Liiiin-hku/smart-scallion-harvester-planter/cad/大葱收种一体机/车架.step

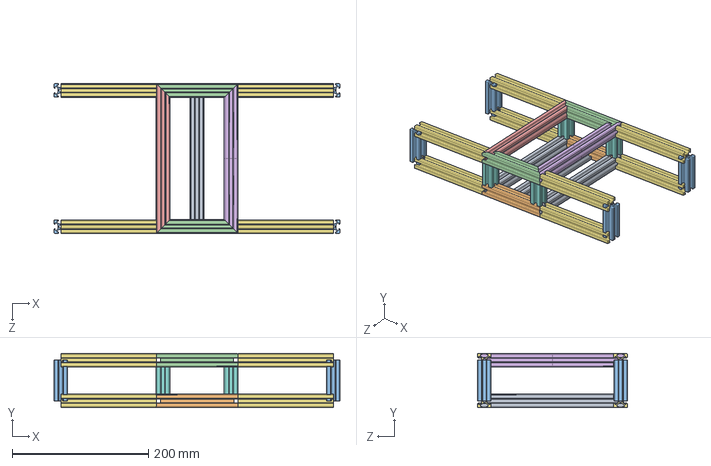
[picture p16: CAD file, 2026-09-12]
cad/大葱收种一体机/车架.step
420.0 x 80.0 x 220.3 mm
