Liiiin-hku/smart-scallion-harvester-planter/cad/大葱收种一体机/不锈钢迷你型CTMA系列气缸[CTMA-16x25-S-CA-SDB]/不锈钢迷你型CTMA系列气缸[CTMA-16x25-S-CA-SDB]_SDB.SLDPRT

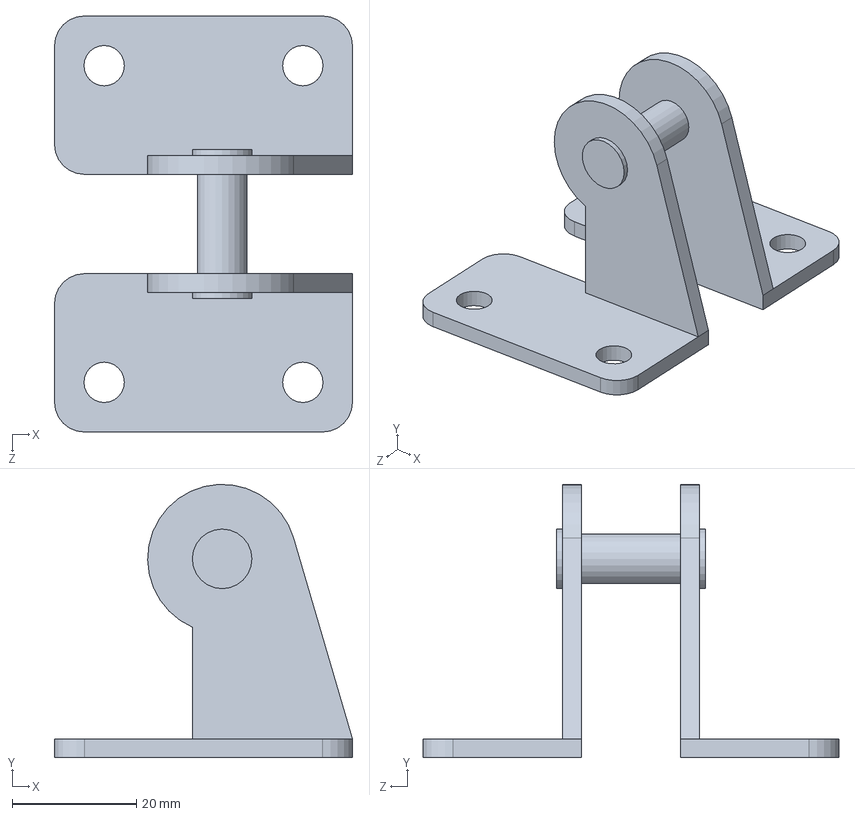
[picture p17: CAD file, 2026-09-12]
cad/大葱收种一体机/不锈钢迷你型CTMA系列气缸[CTMA-16x25-S-CA-SDB]/不锈钢迷你型CTMA系列气缸[CTMA-16x25-S-CA-SDB]_SDB.SLDPRT
48.0 x 44.0 x 67.0 mm
