Liiiin-hku/smart-scallion-harvester-planter/cad/大葱收种一体机/标件/GB╱T 70.2-2015[内六角平圆头螺钉M4×30].step

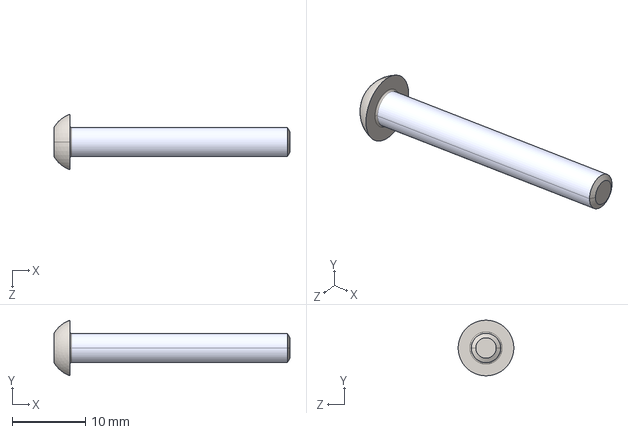
[picture p18: CAD file, 2026-09-12]
cad/大葱收种一体机/标件/GB╱T 70.2-2015[内六角平圆头螺钉M4×30].step
32.2 x 7.60 x 7.60 mm
