Liiiin-hku/smart-scallion-harvester-planter/cad/大葱收种一体机/轮子/21. TYRE.SLDPRT

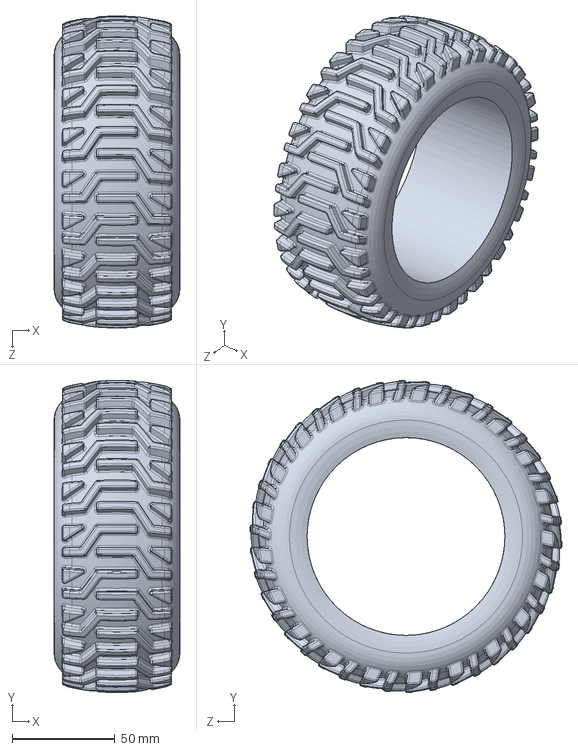
[picture p19: CAD file, 2026-09-12]
cad/大葱收种一体机/轮子/21. TYRE.SLDPRT
61.1 x 151.6 x 151.5 mm
