Liiiin-hku/smart-scallion-harvester-planter/cad/大葱收种一体机/16缸体.step

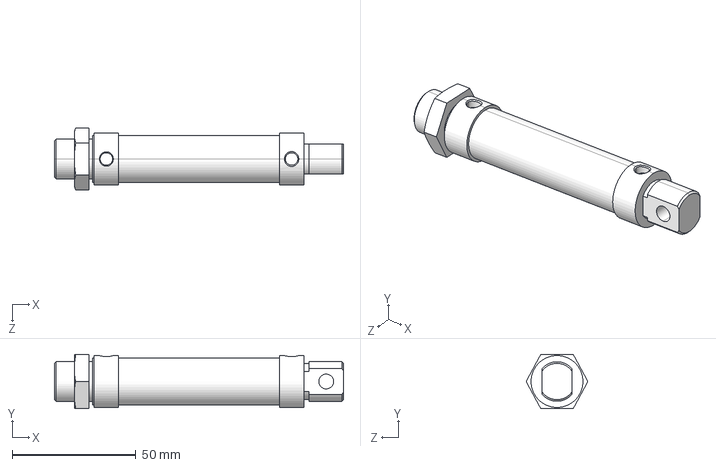
[picture p20: CAD file, 2026-09-12]
cad/大葱收种一体机/16缸体.step
117.0 x 22.0 x 25.0 mm
