Liiiin-hku/smart-scallion-harvester-planter/cad/大葱收种一体机/不锈钢迷你型CTMA系列气缸[CTMA-16x25-S-CA-SDB]/后LB.SLDPRT

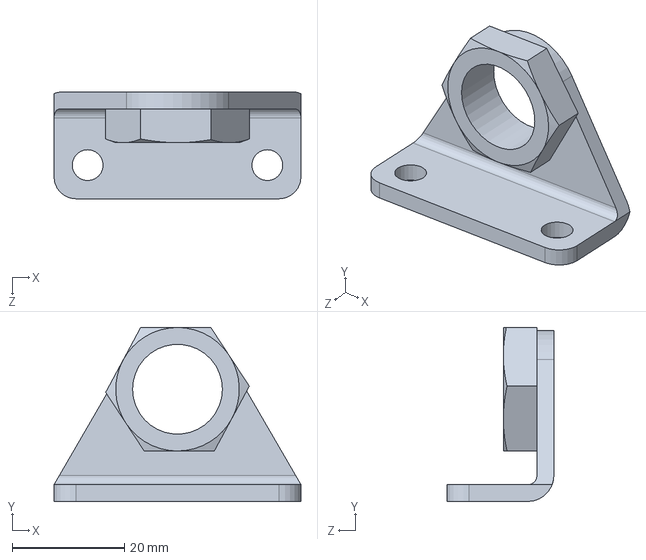
[picture p21: CAD file, 2026-09-12]
cad/大葱收种一体机/不锈钢迷你型CTMA系列气缸[CTMA-16x25-S-CA-SDB]/后LB.SLDPRT
44.0 x 31.0 x 19.0 mm
