Liiiin-hku/smart-scallion-harvester-planter/cad/大葱收种一体机/轮子/19.AXLE.SLDPRT

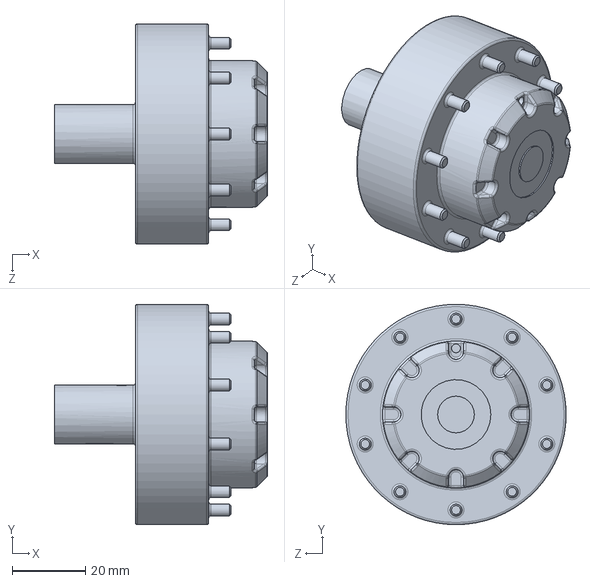
[picture p22: CAD file, 2026-09-12]
cad/大葱收种一体机/轮子/19.AXLE.SLDPRT
58.0 x 60.0 x 60.0 mm
