Liiiin-hku/smart-scallion-harvester-planter/cad/大葱收种一体机/不锈钢迷你型CTMA系列气缸[CTMA-16x25-S-CA-SDB]/活塞杆.SLDPRT

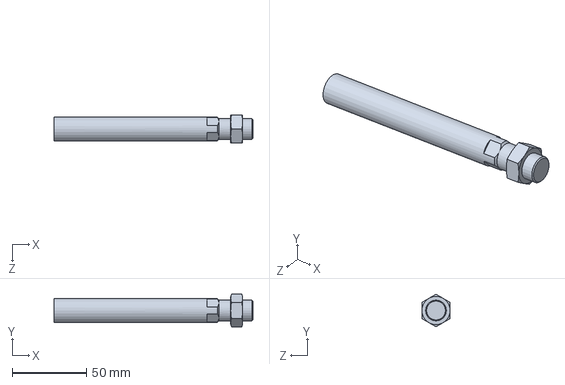
[picture p23: CAD file, 2026-09-12]
cad/大葱收种一体机/不锈钢迷你型CTMA系列气缸[CTMA-16x25-S-CA-SDB]/活塞杆.SLDPRT
134.0 x 21.9 x 19.0 mm
