Liiiin-hku/smart-scallion-harvester-planter/cad/大葱收种一体机/播苗盘.step

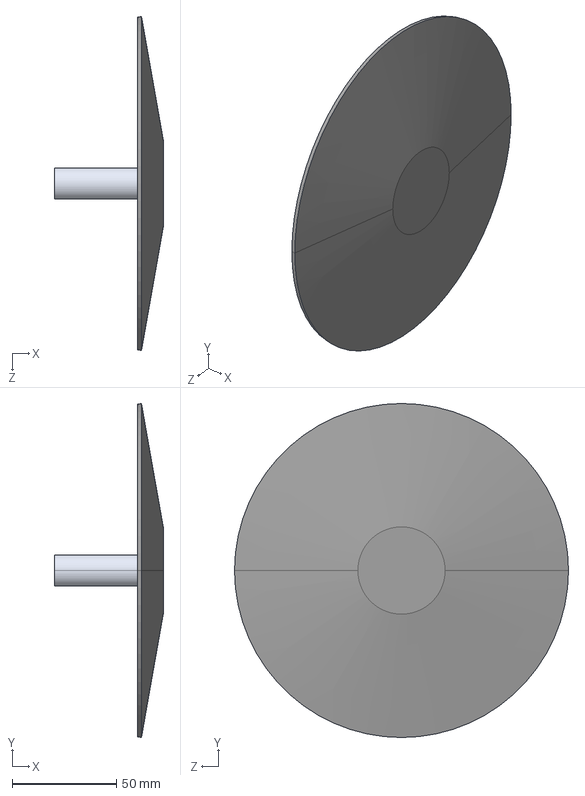
[picture p24: CAD file, 2026-09-12]
cad/大葱收种一体机/播苗盘.step
52.0 x 160.0 x 160.0 mm
