Liiiin-hku/smart-scallion-harvester-planter/cad/大葱收种一体机/标件/GB╱T 276-2013[一面带密封圈（非接触式）的深沟球轴承[60000-RZ]619／6-RZ].step

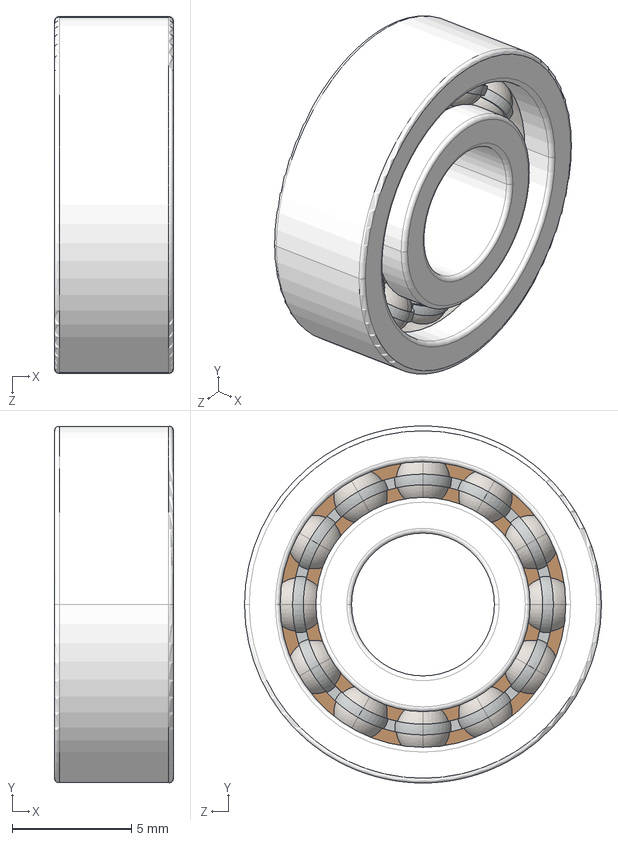
[picture p25: CAD file, 2026-09-12]
cad/大葱收种一体机/标件/GB╱T 276-2013[一面带密封圈（非接触式）的深沟球轴承[60000-RZ]619／6-RZ].step
5.00 x 15.0 x 15.0 mm
