Liiiin-hku/smart-scallion-harvester-planter/cad/大葱收种一体机/轮子/20.RIM.SLDPRT

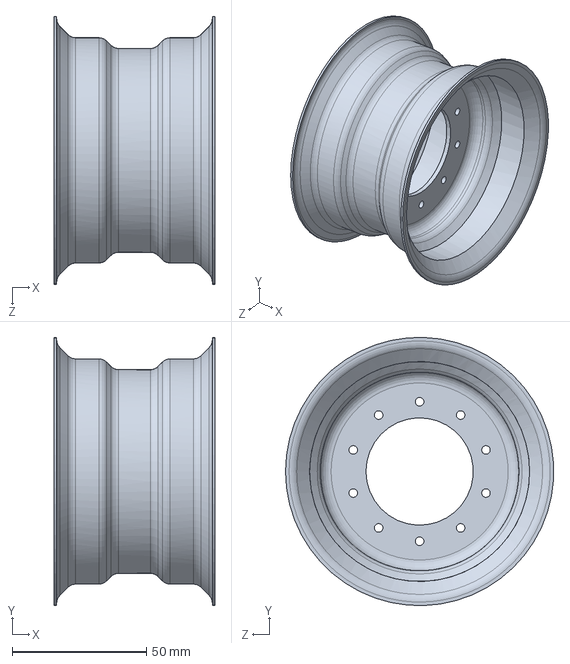
[picture p26: CAD file, 2026-09-12]
cad/大葱收种一体机/轮子/20.RIM.SLDPRT
60.0 x 100.0 x 99.9 mm
