Liiiin-hku/smart-scallion-harvester-planter/cad/大葱收种一体机/1X10X30.step

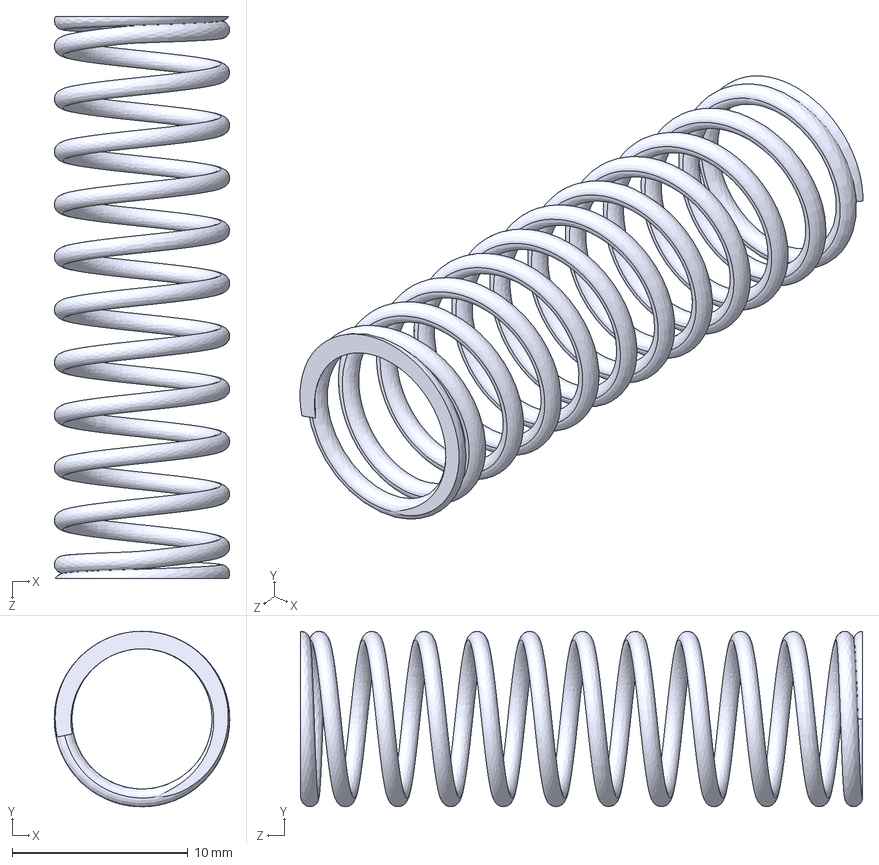
[picture p27: CAD file, 2026-09-12]
cad/大葱收种一体机/1X10X30.step
10.00 x 10.00 x 32.0 mm
