Liiiin-hku/smart-scallion-harvester-planter/cad/大葱收种一体机/不锈钢迷你型CTMA系列气缸[CTMA-16x25-S-CA-SDB]/不锈钢迷你型CTMA系列气缸[CTMA-16x25-S-CA-SDB]_16缸体.SLDPRT

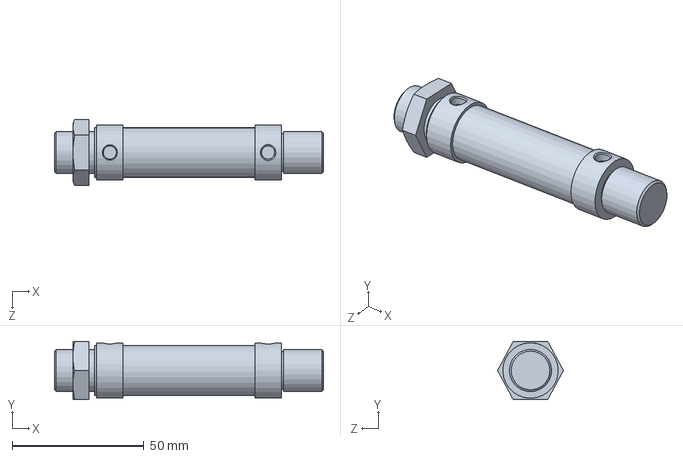
[picture p28: CAD file, 2026-09-12]
cad/大葱收种一体机/不锈钢迷你型CTMA系列气缸[CTMA-16x25-S-CA-SDB]/不锈钢迷你型CTMA系列气缸[CTMA-16x25-S-CA-SDB]_16缸体.SLDPRT
102.0 x 22.0 x 25.0 mm
