Liiiin-hku/smart-scallion-harvester-planter/cad/大葱收种一体机/盘.step

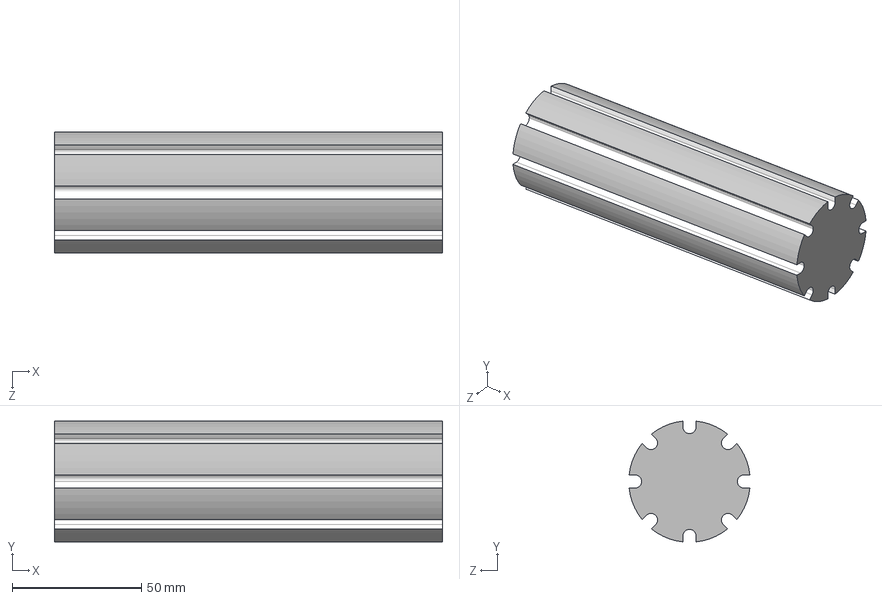
[picture p29: CAD file, 2026-09-12]
cad/大葱收种一体机/盘.step
150.0 x 46.7 x 46.7 mm
