Liiiin-hku/smart-scallion-harvester-planter/cad/大葱收种一体机/不锈钢迷你型CTMA系列气缸[CTMA-16x25-S-CA-SDB]/不锈钢迷你型CTMA系列气缸[CTMA-16x25-S-CA-SDB]_16活塞杆.SLDPRT

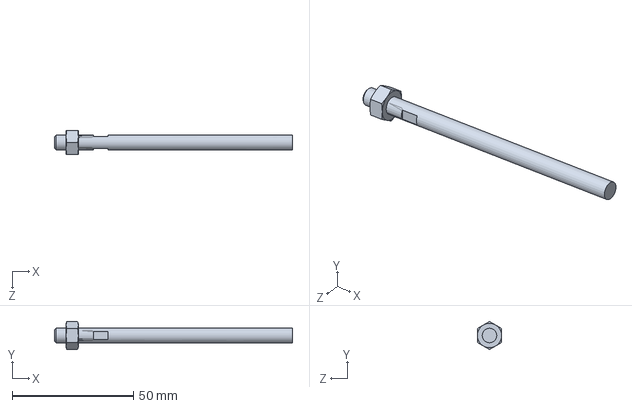
[picture p30: CAD file, 2026-09-12]
cad/大葱收种一体机/不锈钢迷你型CTMA系列气缸[CTMA-16x25-S-CA-SDB]/不锈钢迷你型CTMA系列气缸[CTMA-16x25-S-CA-SDB]_16活塞杆.SLDPRT
98.0 x 11.5 x 10.0 mm
