Liiiin-hku/smart-scallion-harvester-planter/cad/大葱收种一体机/电源.step

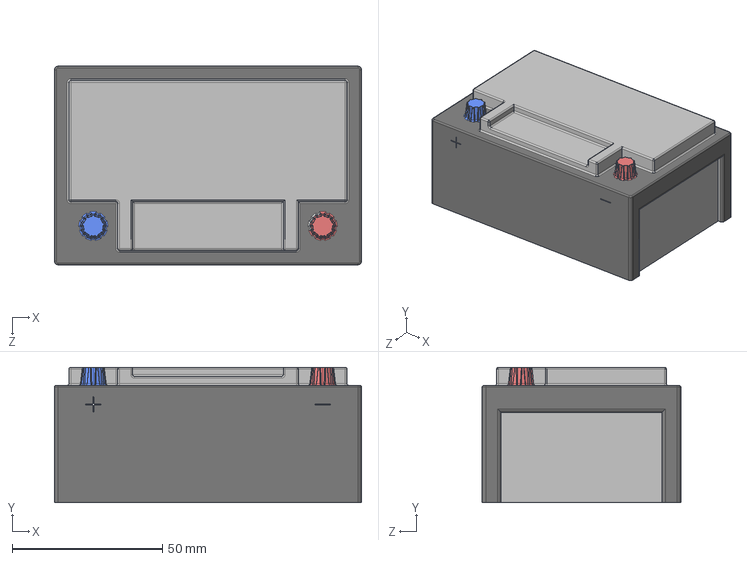
[picture p34: CAD file, 2026-09-12]
cad/大葱收种一体机/电源.step
102.0 x 45.0 x 66.0 mm
