Liiiin-hku/smart-scallion-harvester-planter/cad/大葱收种一体机/气缸座.step

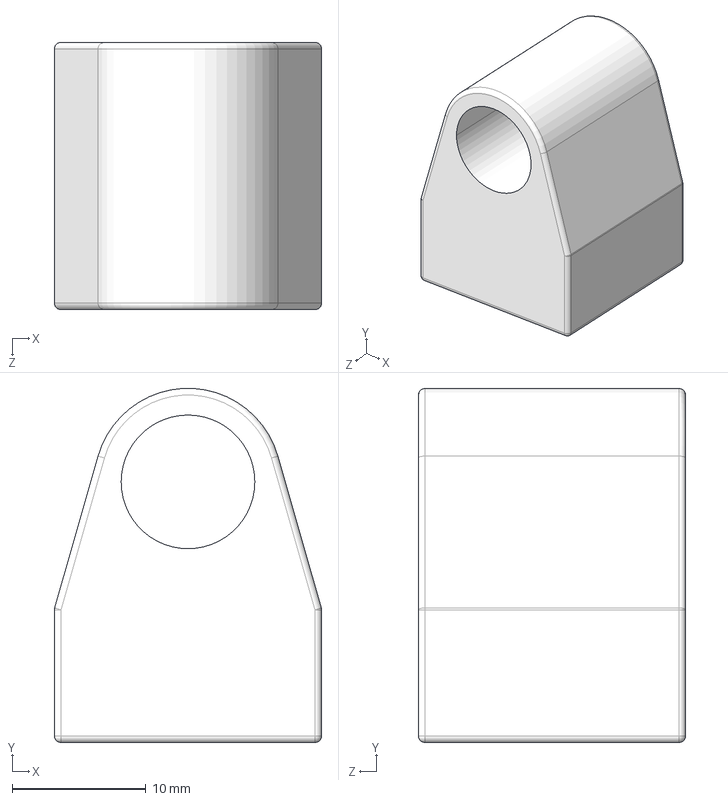
[picture p35: CAD file, 2026-09-12]
cad/大葱收种一体机/气缸座.step
20.0 x 26.5 x 20.0 mm
