Liiiin-hku/smart-scallion-harvester-planter/cad/大葱收种一体机/M3螺母.step

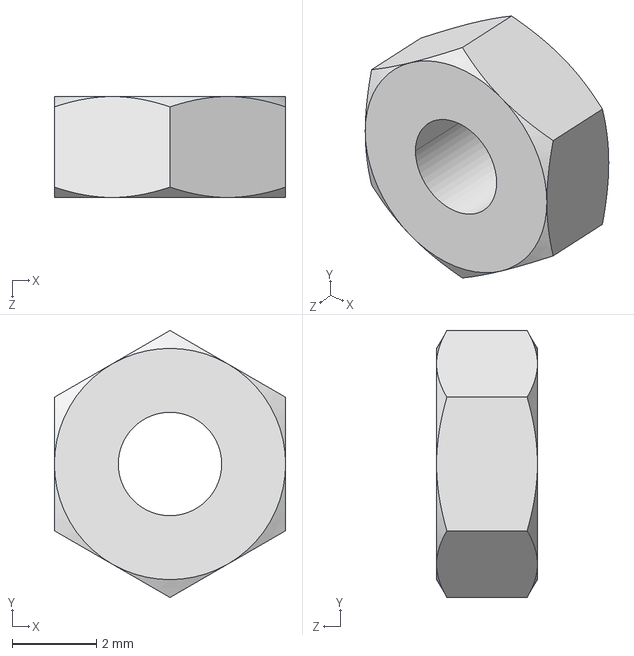
[picture p36: CAD file, 2026-09-12]
cad/大葱收种一体机/M3螺母.step
5.50 x 6.35 x 2.40 mm
