Liiiin-hku/smart-scallion-harvester-planter/cad/大葱收种一体机/标件/M4螺母.step

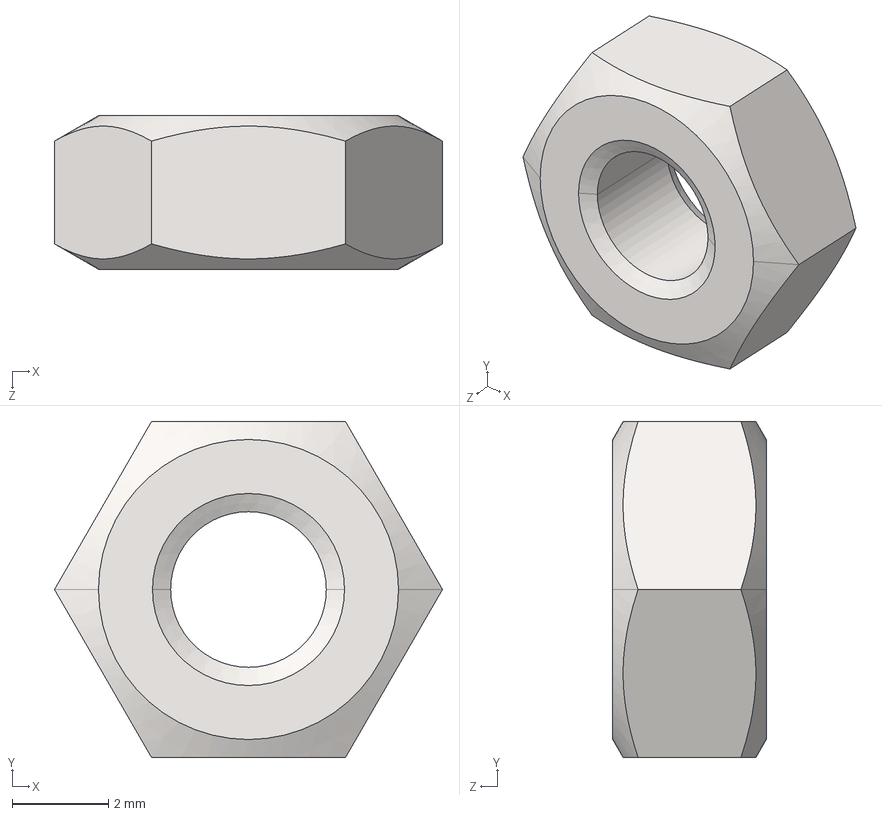
[picture p39: CAD file, 2026-09-12]
cad/大葱收种一体机/标件/M4螺母.step
8.08 x 7.00 x 3.20 mm
