Liiiin-hku/smart-scallion-harvester-planter/cad/大葱收种一体机/起垄.step

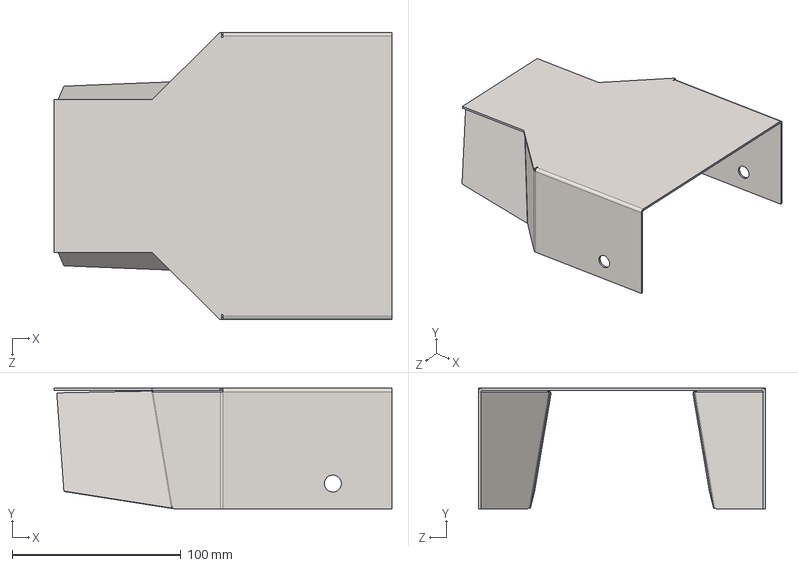
[picture p40: CAD file, 2026-09-12]
cad/大葱收种一体机/起垄.step
200.0 x 71.5 x 170.0 mm
