Liiiin-hku/smart-scallion-harvester-planter/cad/大葱收种一体机/标件/11x5t5.step

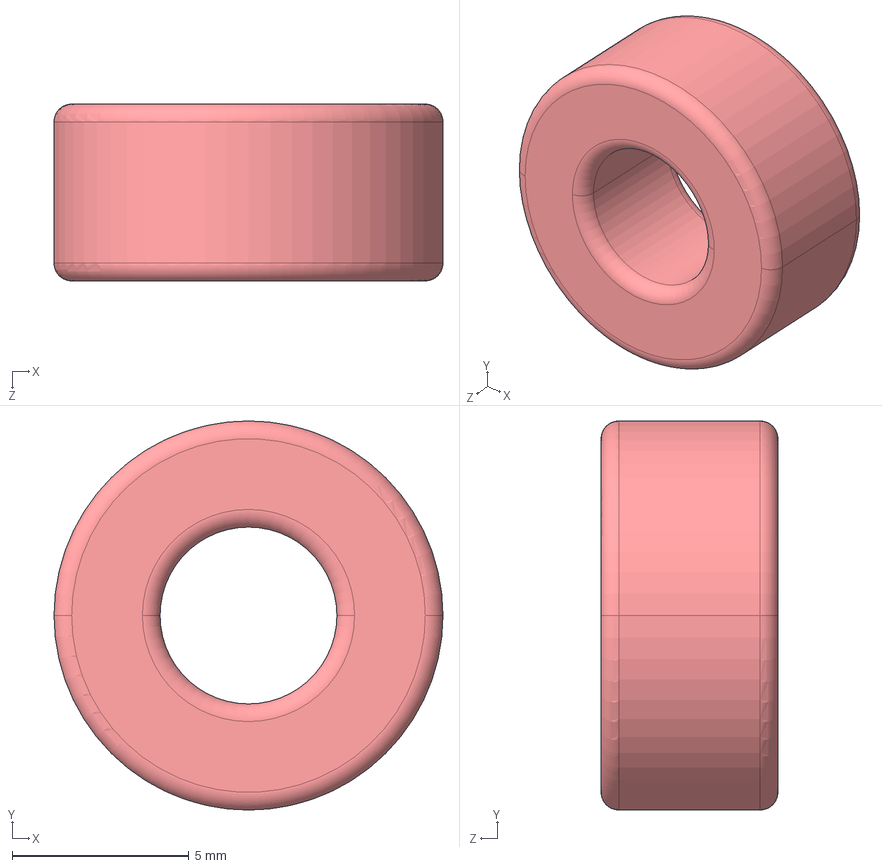
[picture p41: CAD file, 2026-09-12]
cad/大葱收种一体机/标件/11x5t5.step
11.0 x 11.0 x 5.00 mm
