Liiiin-hku/smart-scallion-harvester-planter/cad/大葱收种一体机/输送带导向滚轴.step

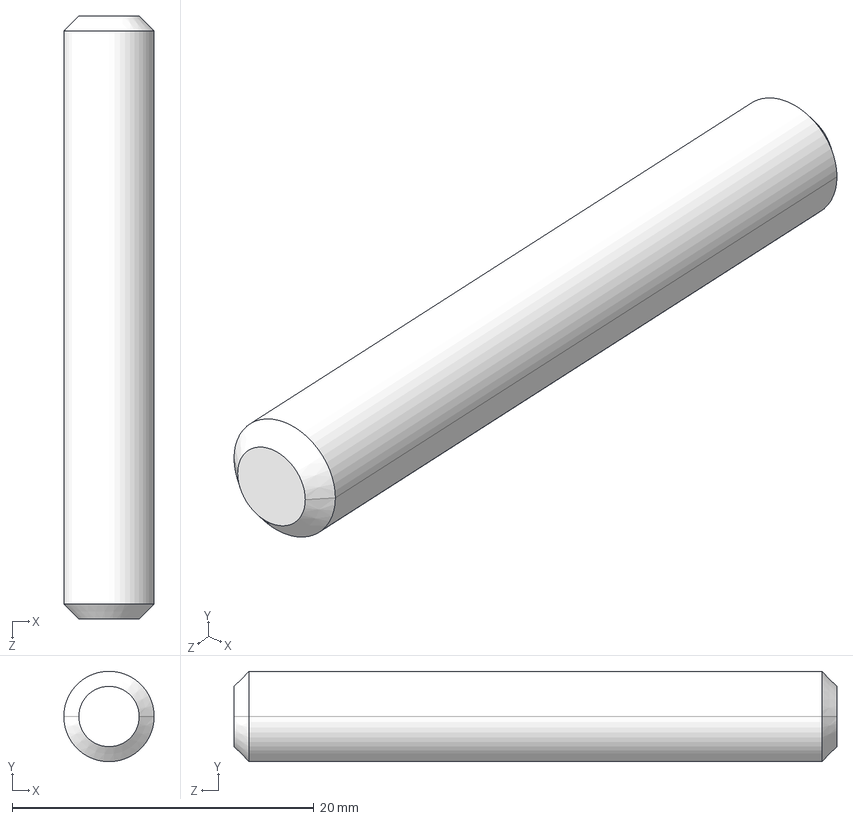
[picture p42: CAD file, 2026-09-12]
cad/大葱收种一体机/输送带导向滚轴.step
6.00 x 6.00 x 40.0 mm
