Liiiin-hku/smart-scallion-harvester-planter/cad/大葱收种一体机/标件/GB╱T 9074.1-2002[十字槽盘头螺钉（S3）和平垫圈组合件M3×8 10.9 S3 N].step

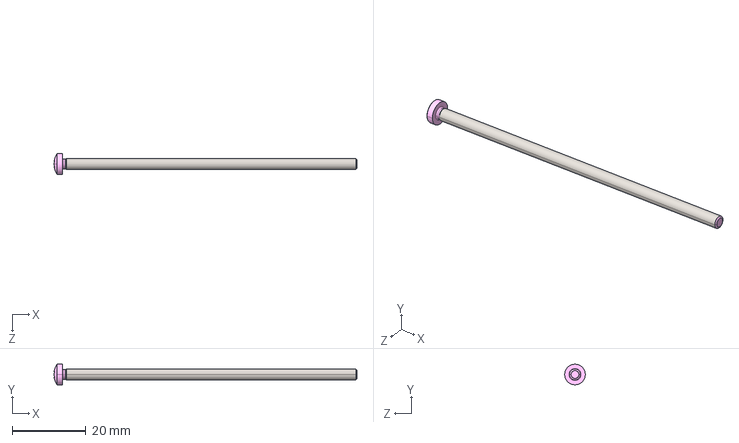
[picture p43: CAD file, 2026-09-12]
cad/大葱收种一体机/标件/GB╱T 9074.1-2002[十字槽盘头螺钉（S3）和平垫圈组合件M3×8 10.9 S3 N].step
82.4 x 5.60 x 5.60 mm
