Liiiin-hku/smart-scallion-harvester-planter/cad/大葱收种一体机/气缸座 3.step

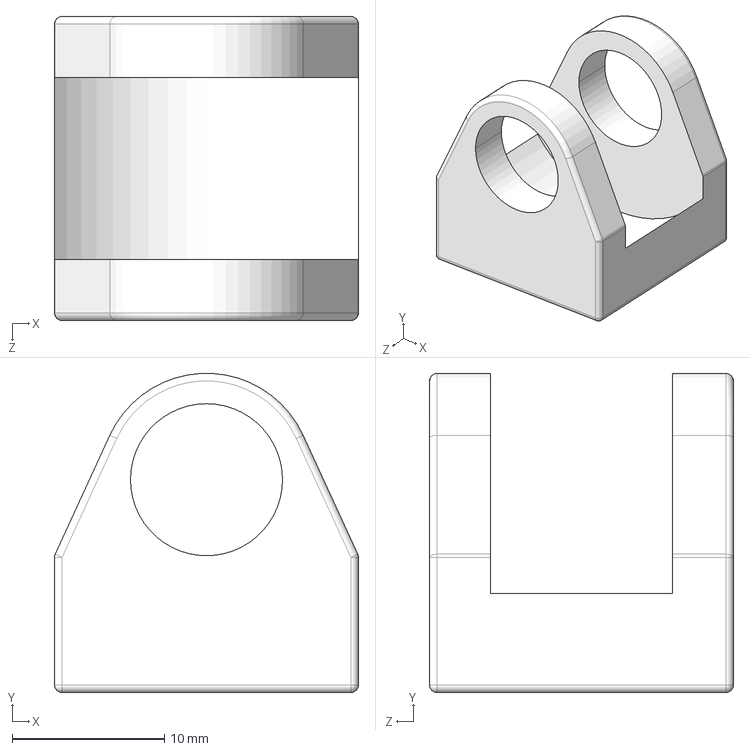
[picture p44: CAD file, 2026-09-12]
cad/大葱收种一体机/气缸座 3.step
20.0 x 21.0 x 20.0 mm
