Liiiin-hku/smart-scallion-harvester-planter/cad/大葱收种一体机/_CT2-20-2020.step.step

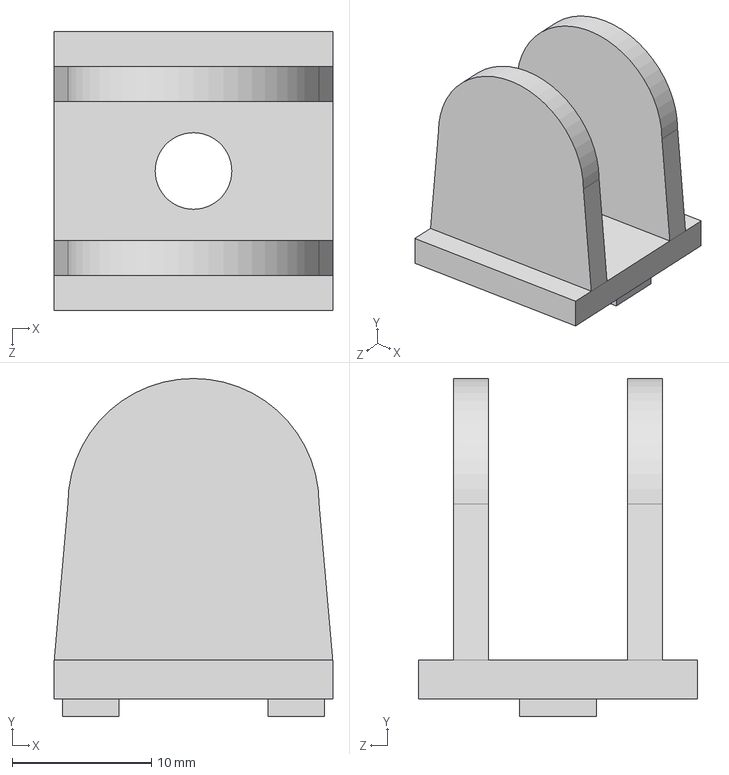
[picture p45: CAD file, 2026-09-12]
cad/大葱收种一体机/_CT2-20-2020.step.step
20.0 x 24.3 x 20.0 mm
