Liiiin-hku/smart-scallion-harvester-planter/cad/大葱收种一体机/标件/GB╱T 6186-2000[2型全金属六角锁紧螺母 9级M5].step

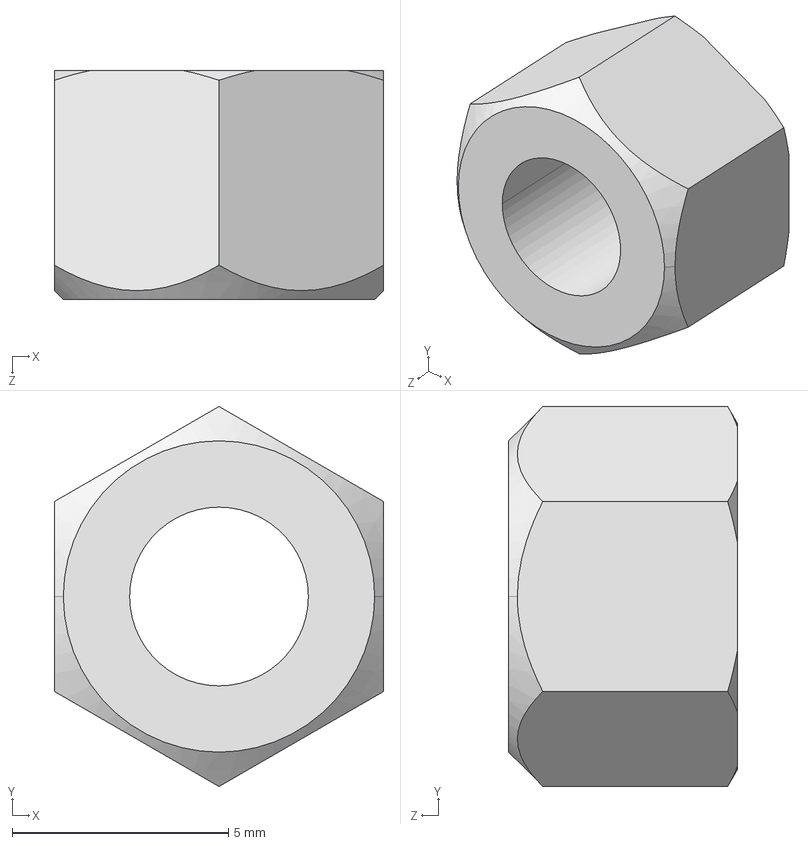
[picture p46: CAD file, 2026-09-12]
cad/大葱收种一体机/标件/GB╱T 6186-2000[2型全金属六角锁紧螺母 9级M5].step
7.61 x 8.79 x 5.30 mm
