Liiiin-hku/smart-scallion-harvester-planter/cad/大葱收种一体机/标件/垫片5.5x10t0.5.step

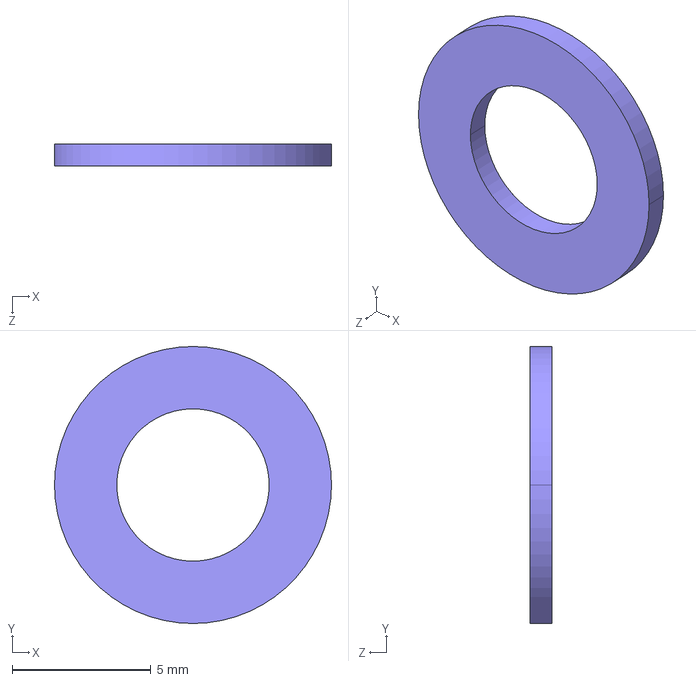
[picture p47: CAD file, 2026-09-12]
cad/大葱收种一体机/标件/垫片5.5x10t0.5.step
10.0 x 10.0 x 0.8 mm
