Liiiin-hku/smart-scallion-harvester-planter/cad/大葱收种一体机/传送带轴固定调节座2.step

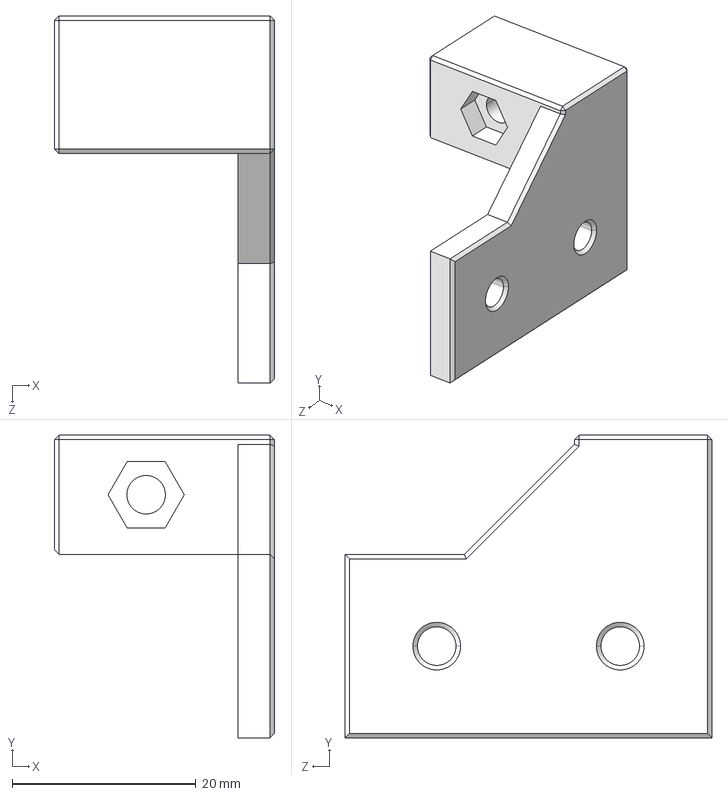
[picture p49: CAD file, 2026-09-12]
cad/大葱收种一体机/传送带轴固定调节座2.step
24.0 x 33.0 x 40.0 mm
