Liiiin-hku/smart-scallion-harvester-planter/cad/大葱收种一体机/T型螺母[AENT20-4].step

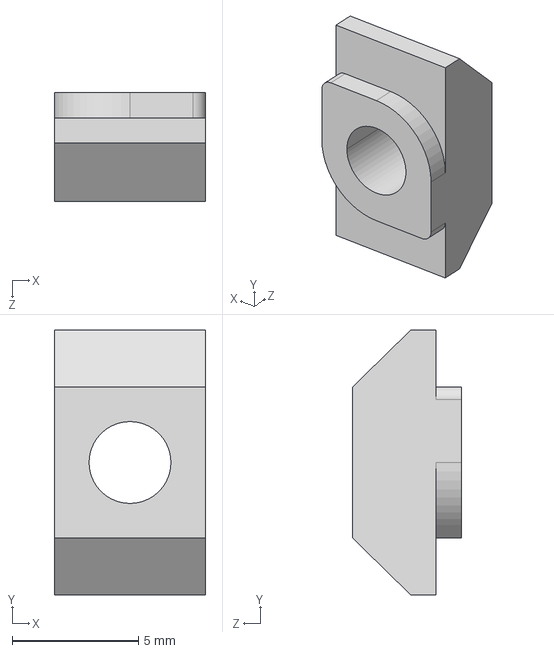
[picture p50: CAD file, 2026-09-12]
cad/大葱收种一体机/T型螺母[AENT20-4].step
6.00 x 10.5 x 4.30 mm
