Liiiin-hku/smart-scallion-harvester-planter/cad/大葱收种一体机/标件/17x26t5.step

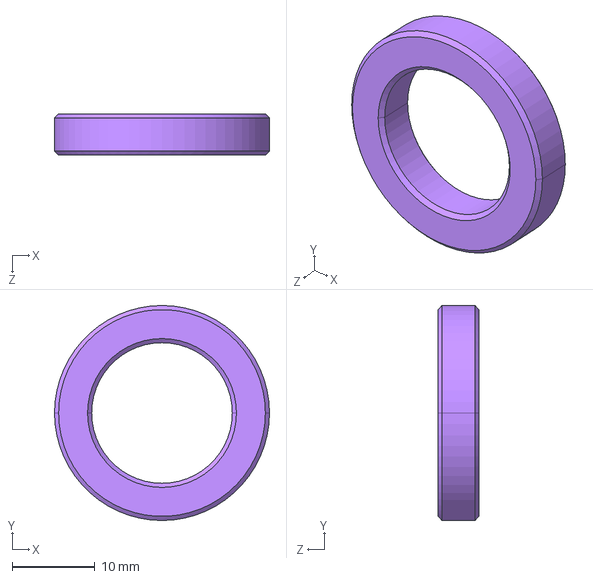
[picture p51: CAD file, 2026-09-12]
cad/大葱收种一体机/标件/17x26t5.step
26.0 x 26.0 x 5.00 mm
