Liiiin-hku/smart-scallion-harvester-planter/cad/大葱收种一体机/标件/内六角螺栓[AEB6-18].step

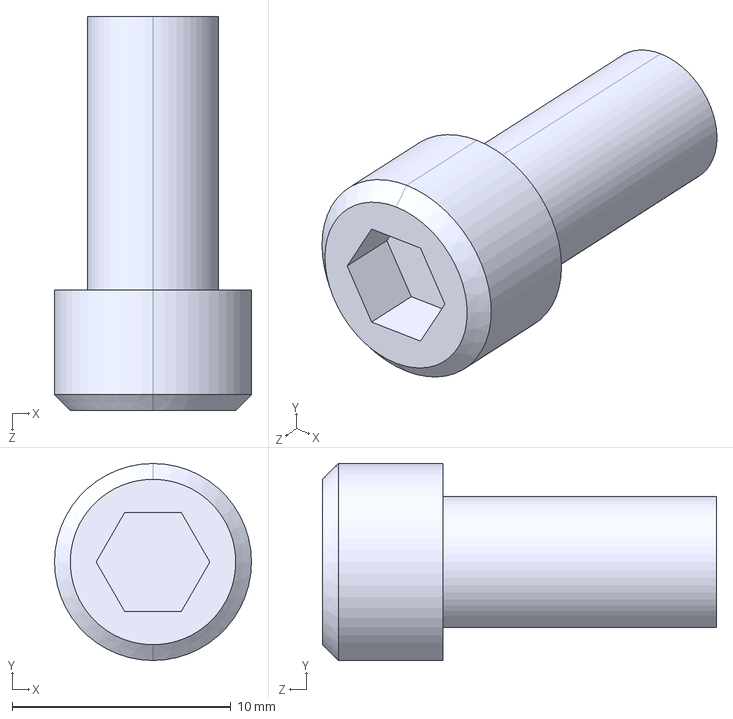
[picture p53: CAD file, 2026-09-12]
cad/大葱收种一体机/标件/内六角螺栓[AEB6-18].step
9.00 x 9.00 x 18.0 mm
