Liiiin-hku/smart-scallion-harvester-planter/cad/大葱收种一体机/弹簧座2.step

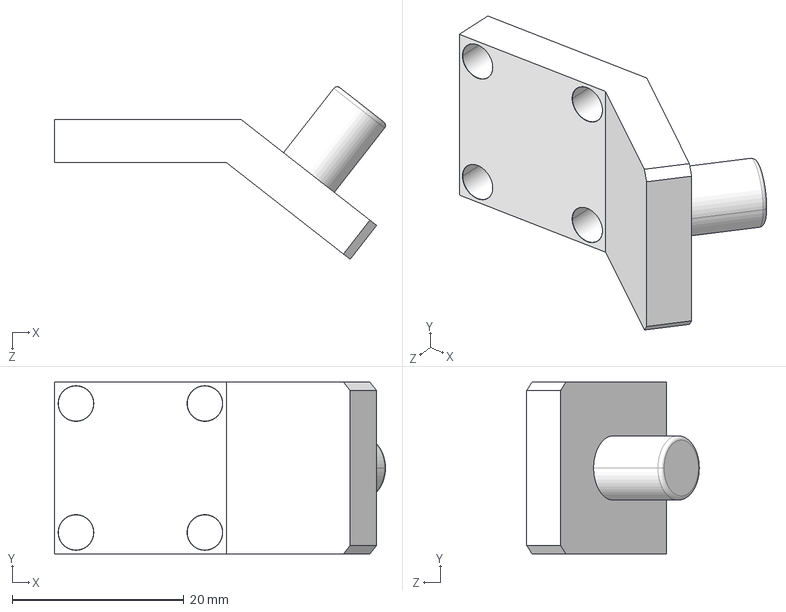
[picture p54: CAD file, 2026-09-12]
cad/大葱收种一体机/弹簧座2.step
38.5 x 20.0 x 20.1 mm
