Liiiin-hku/smart-scallion-harvester-planter/cad/大葱收种一体机/标件/GB╱T 6186-2000[2型全金属六角锁紧螺母 9级M6].step

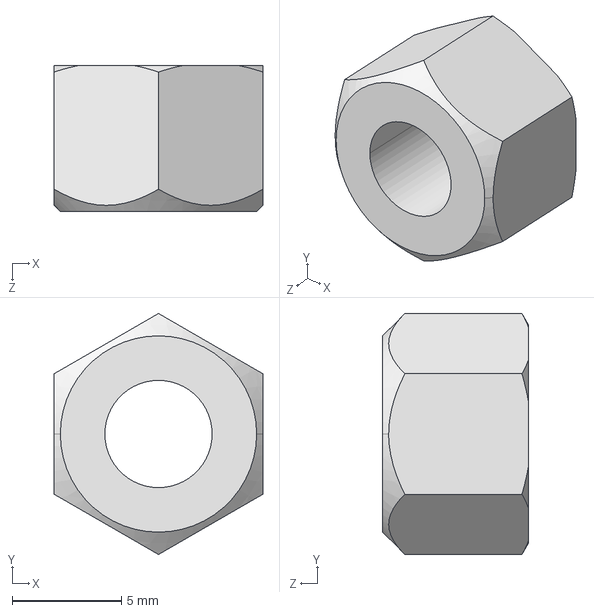
[picture p55: CAD file, 2026-09-12]
cad/大葱收种一体机/标件/GB╱T 6186-2000[2型全金属六角锁紧螺母 9级M6].step
9.57 x 11.1 x 6.70 mm
