Liiiin-hku/smart-scallion-harvester-planter/cad/大葱收种一体机/GB╱T 819.1-2016[十字槽沉头螺钉M3×25].step

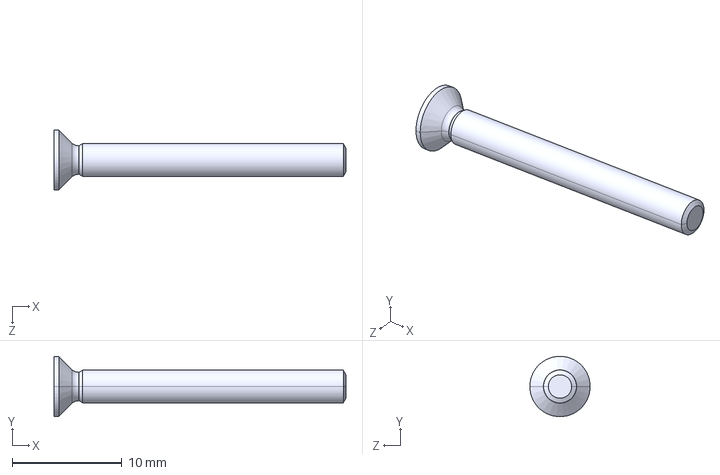
[picture p56: CAD file, 2026-09-12]
cad/大葱收种一体机/GB╱T 819.1-2016[十字槽沉头螺钉M3×25].step
26.6 x 5.50 x 5.50 mm
