Liiiin-hku/smart-scallion-harvester-planter/cad/大葱收种一体机/标件/特殊螺钉 小径内六角圆柱头螺钉[PSGS-M8-30-B].step

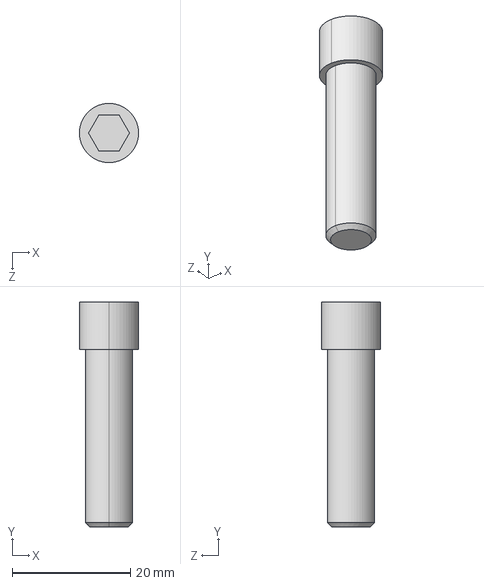
[picture p57: CAD file, 2026-09-12]
cad/大葱收种一体机/标件/特殊螺钉 小径内六角圆柱头螺钉[PSGS-M8-30-B].step
10.0 x 38.0 x 10.0 mm
