Liiiin-hku/smart-scallion-harvester-planter/cad/大葱收种一体机/输送带导向滚2固定亚克力板.step

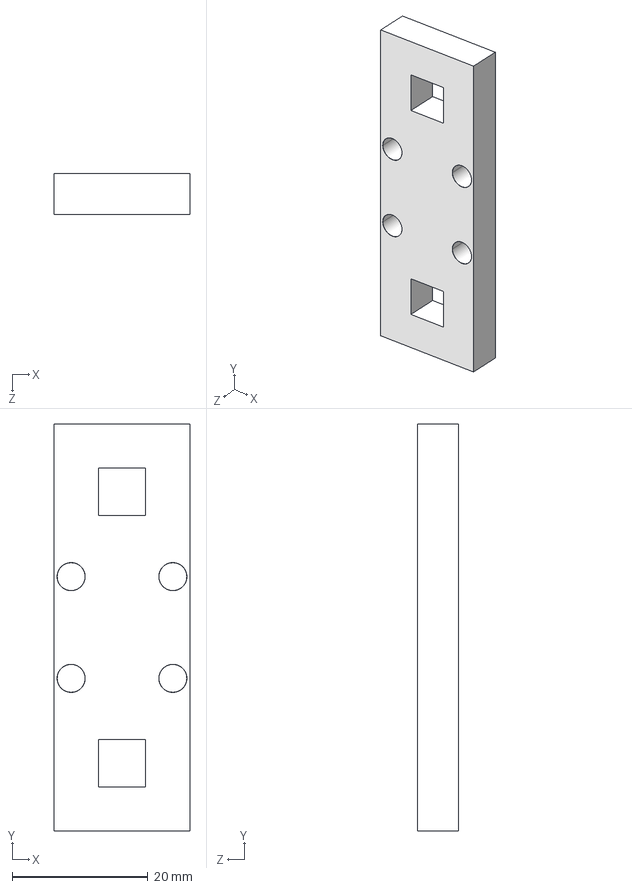
[picture p58: CAD file, 2026-09-12]
cad/大葱收种一体机/输送带导向滚2固定亚克力板.step
20.0 x 60.0 x 6.00 mm
