Liiiin-hku/smart-scallion-harvester-planter/cad/大葱收种一体机/松土铲刀.step

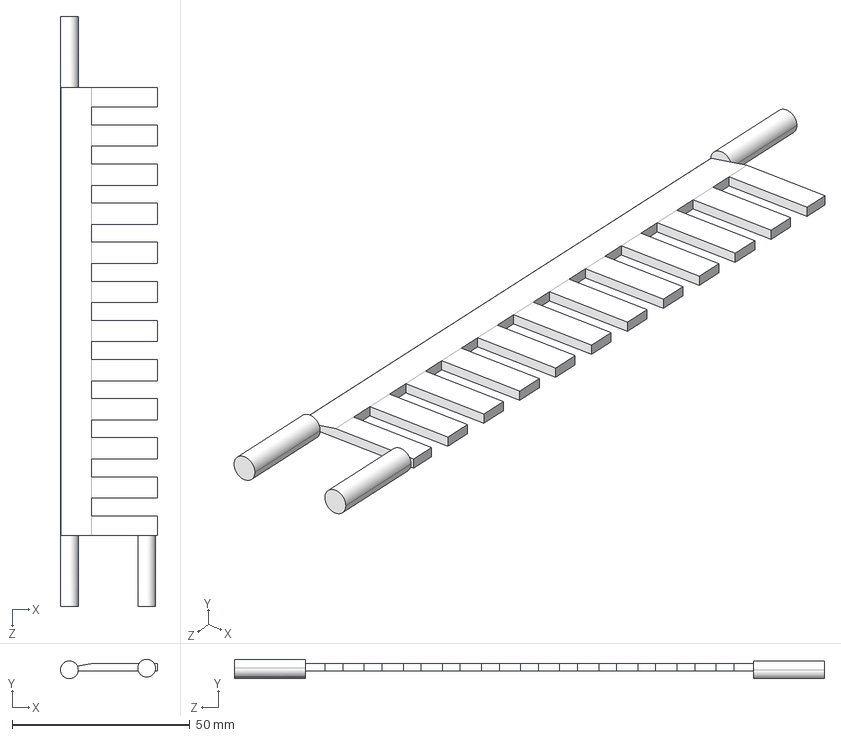
[picture p59: CAD file, 2026-09-12]
cad/大葱收种一体机/松土铲刀.step
27.4 x 5.46 x 166.0 mm
