Liiiin-hku/smart-scallion-harvester-planter/cad/大葱收种一体机/标件/20系列2020压铸角铝[CB-20-2020].step

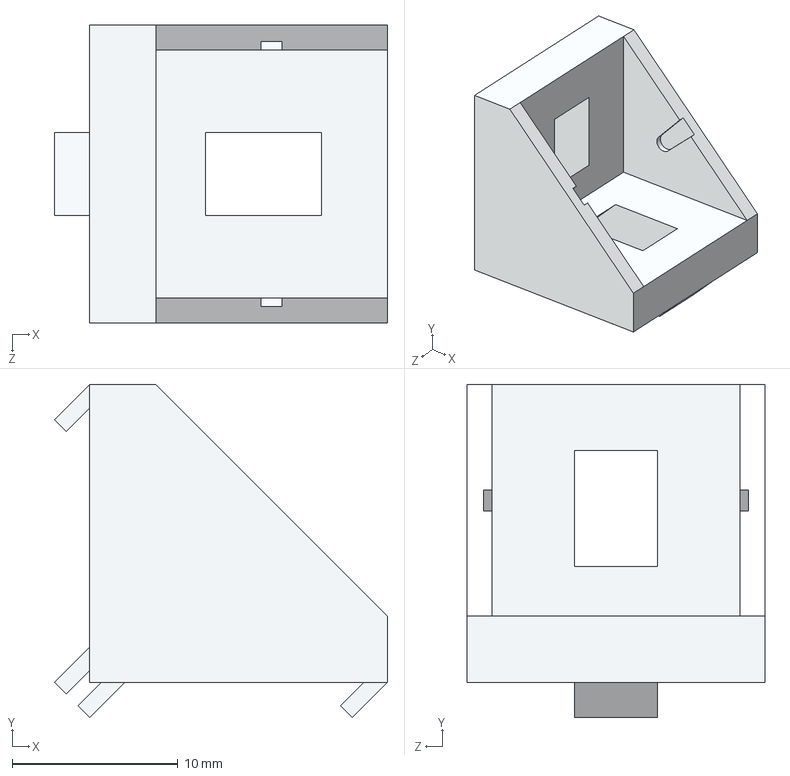
[picture p60: CAD file, 2026-09-12]
cad/大葱收种一体机/标件/20系列2020压铸角铝[CB-20-2020].step
20.1 x 20.1 x 18.0 mm
