Liiiin-hku/smart-scallion-harvester-planter/cad/大葱收种一体机/标件/GB╱T 95-2002[平垫圈 C级3].step

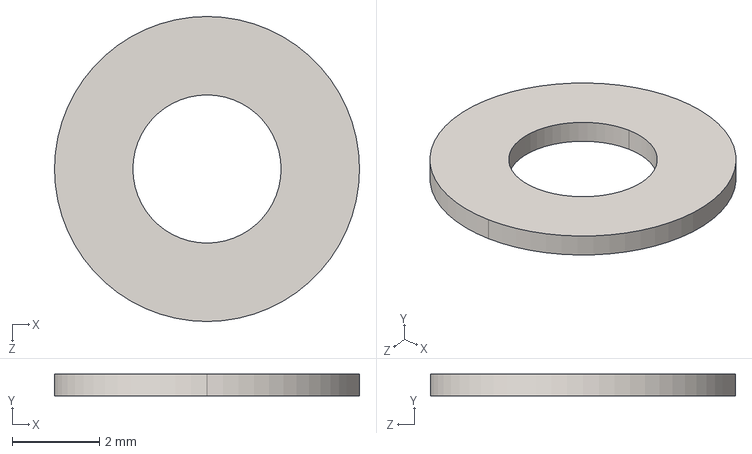
[picture p61: CAD file, 2026-09-12]
cad/大葱收种一体机/标件/GB╱T 95-2002[平垫圈 C级3].step
7.00 x 0.5 x 7.00 mm
