Liiiin-hku/smart-scallion-harvester-planter/cad/大葱收种一体机/播种部分.step

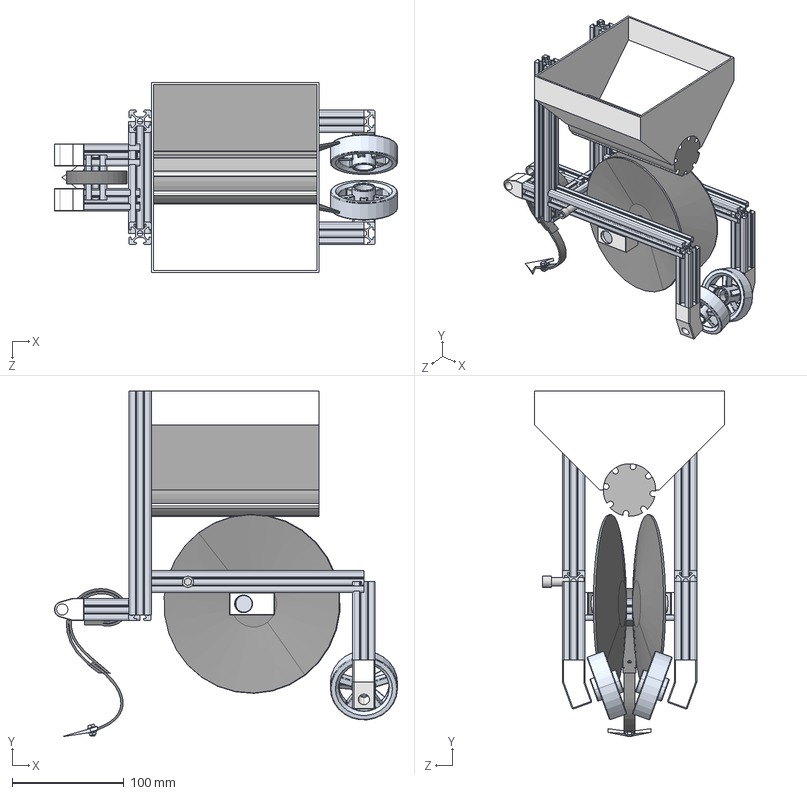
[picture p62: CAD file, 2026-09-12]
cad/大葱收种一体机/播种部分.step
306.5 x 308.8 x 170.0 mm
储存箱子
攫
畦醮攫 x 2
Spike Gribe
储存箱子支撑_默认<按加工>
嘐隅釱 x 2
特殊螺钉 小径内六角圆柱头螺钉[PSGS-M8-30-B]
ァ詰釱2 x 2
蛹笭謫 x 2
负重轮座 x 2
