Liiiin-hku/smart-scallion-harvester-planter/cad/大葱收种一体机/大葱.step

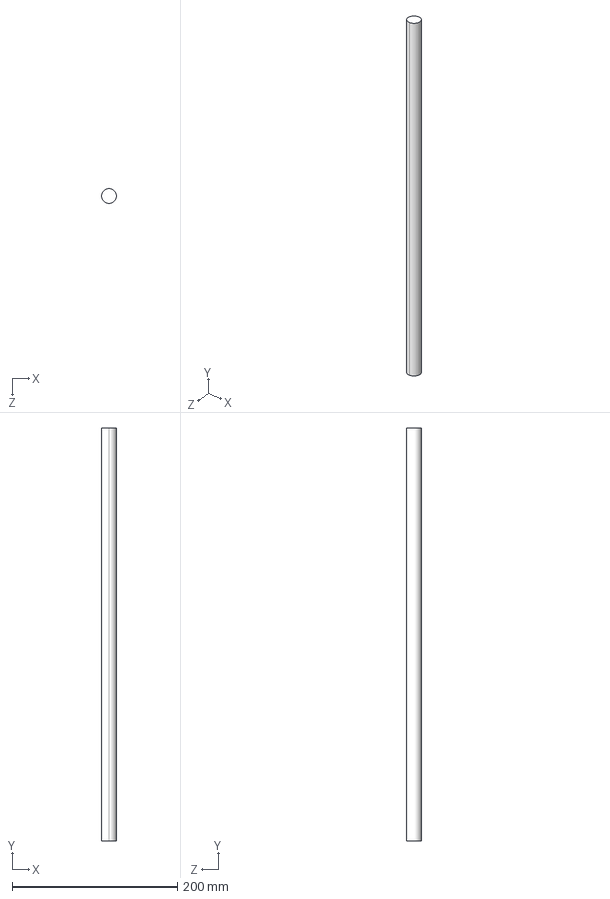
[picture p63: CAD file, 2026-09-12]
cad/大葱收种一体机/大葱.step
18.0 x 500.0 x 18.0 mm
