Liiiin-hku/smart-scallion-harvester-planter/cad/大葱收种一体机/扶葱.step

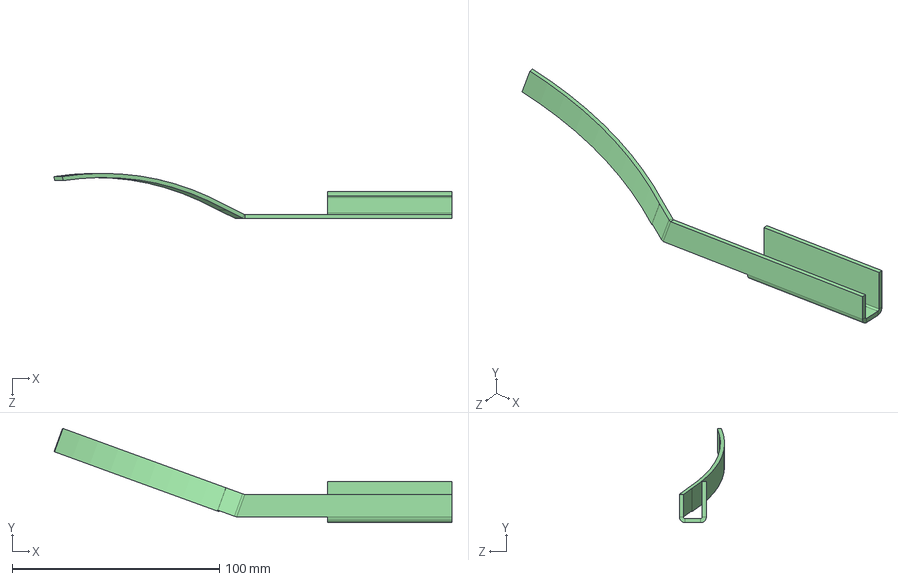
[picture p64: CAD file, 2026-09-12]
cad/大葱收种一体机/扶葱.step
192.1 x 45.6 x 21.8 mm
