Liiiin-hku/smart-scallion-harvester-planter/cad/大葱收种一体机/传送带轴固定调节电机座.step

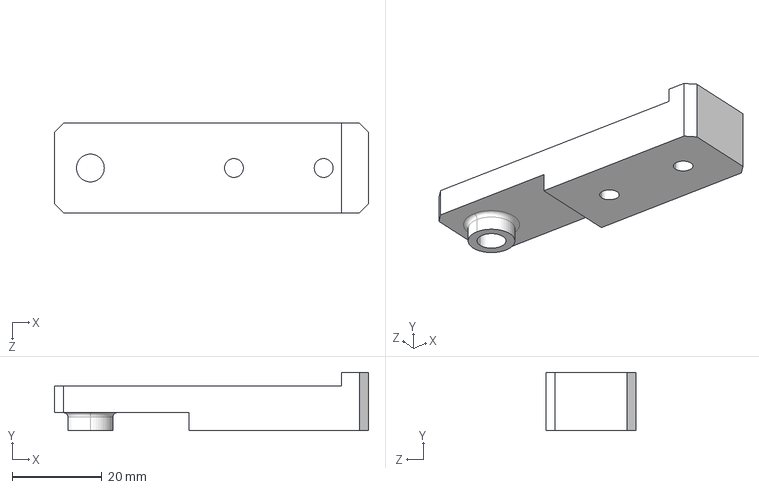
[picture p65: CAD file, 2026-09-12]
cad/大葱收种一体机/传送带轴固定调节电机座.step
70.0 x 13.0 x 20.0 mm
