Liiiin-hku/smart-scallion-harvester-planter/cad/大葱收种一体机/传送带轴固定座.step

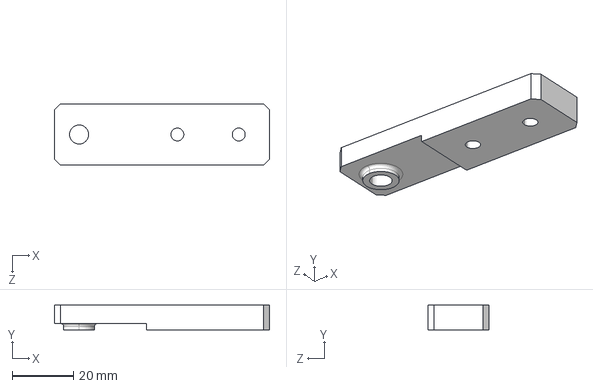
[picture p67: CAD file, 2026-09-12]
cad/大葱收种一体机/传送带轴固定座.step
70.0 x 8.00 x 20.0 mm
