Liiiin-hku/smart-scallion-harvester-planter/cad/大葱收种一体机/输送带导向滚2.step

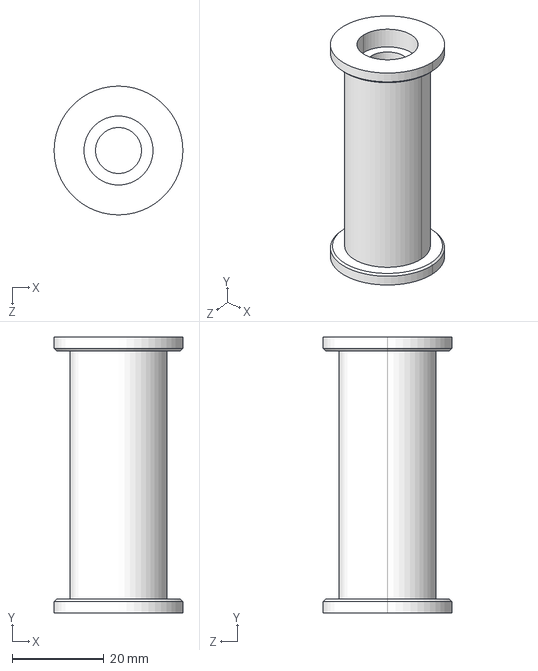
[picture p68: CAD file, 2026-09-12]
cad/大葱收种一体机/输送带导向滚2.step
28.0 x 60.0 x 28.0 mm
