Liiiin-hku/smart-scallion-harvester-planter/cad/大葱收种一体机/负重轮.step

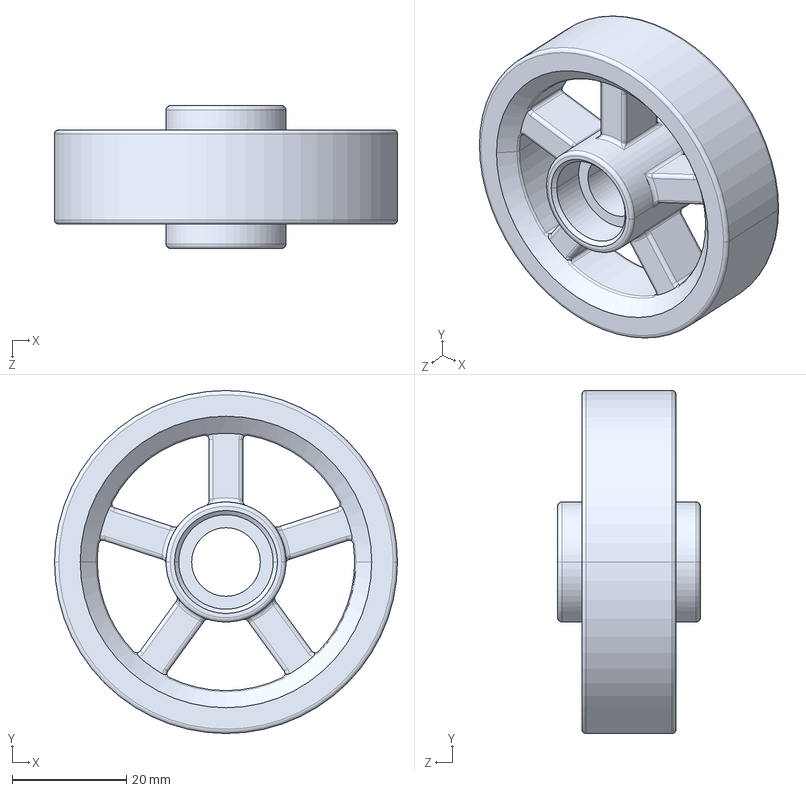
[picture p69: CAD file, 2026-09-12]
cad/大葱收种一体机/负重轮.step
60.0 x 60.0 x 25.0 mm
