Liiiin-hku/smart-scallion-harvester-planter/cad/大葱收种一体机/松土铲刀固定.step

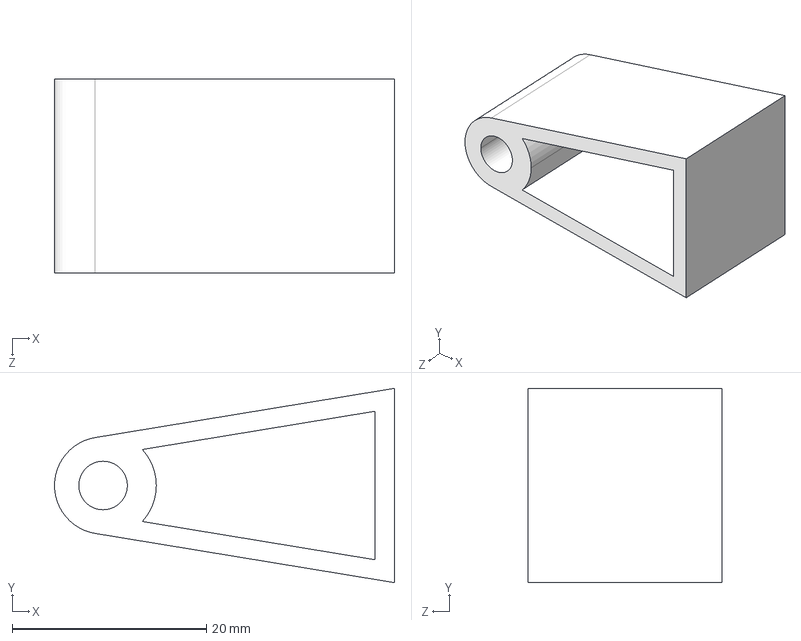
[picture p70: CAD file, 2026-09-12]
cad/大葱收种一体机/松土铲刀固定.step
35.0 x 20.0 x 20.0 mm
