Liiiin-hku/smart-scallion-harvester-planter/cad/大葱收种一体机/输送带导向滚.step

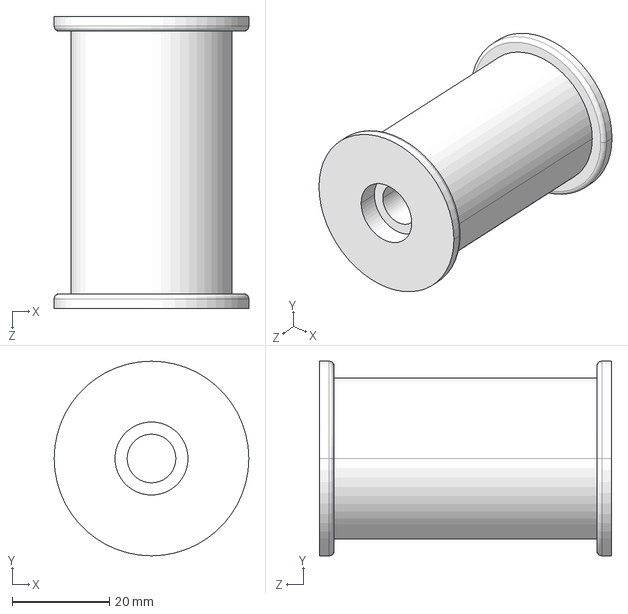
[picture p71: CAD file, 2026-09-12]
cad/大葱收种一体机/输送带导向滚.step
40.0 x 40.0 x 60.0 mm
