Liiiin-hku/smart-scallion-harvester-planter/cad/大葱收种一体机/输送带导向滚 动力.step

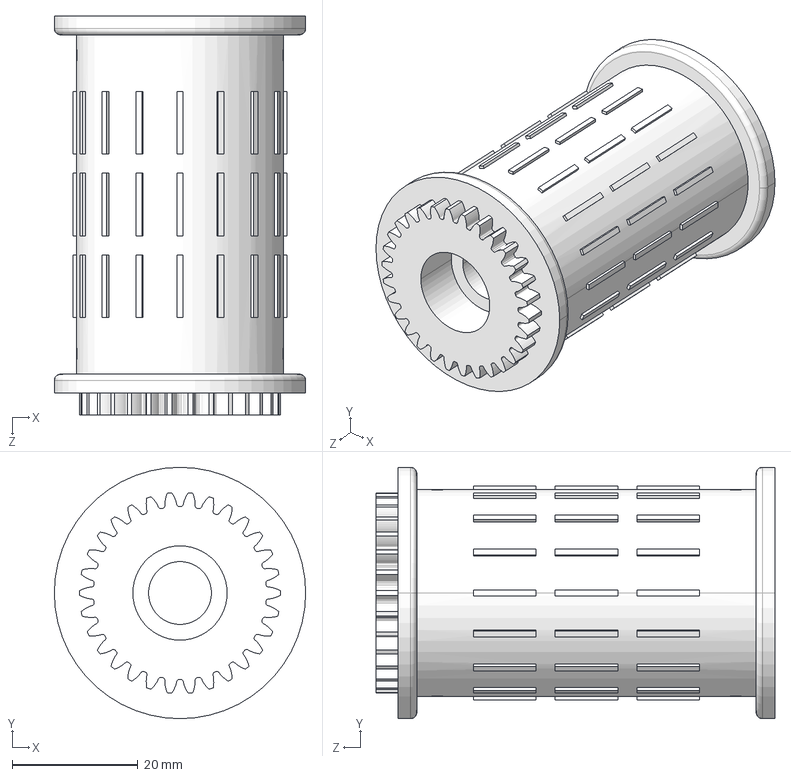
[picture p72: CAD file, 2026-09-12]
cad/大葱收种一体机/输送带导向滚 动力.step
40.0 x 40.0 x 63.5 mm
