Liiiin-hku/smart-scallion-harvester-planter/cad/大葱收种一体机/传送带轴固定座2.step

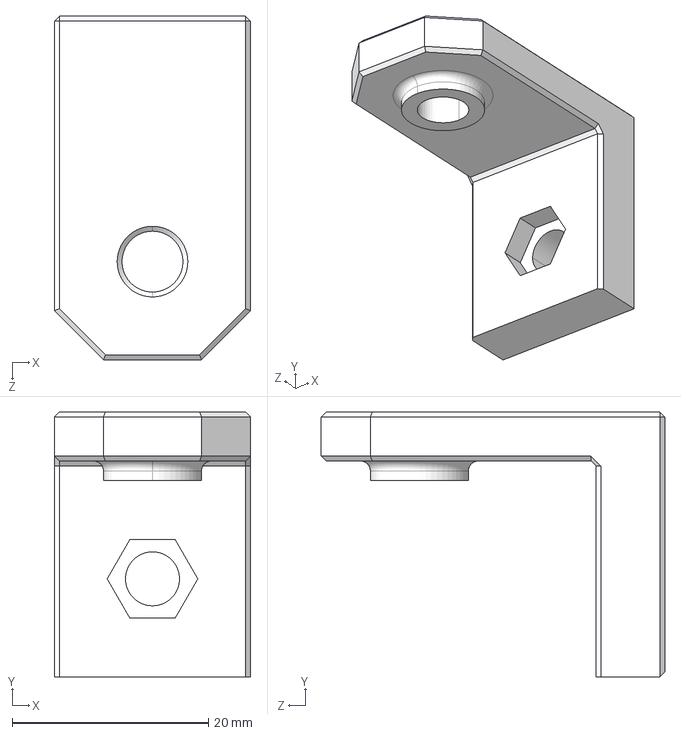
[picture p73: CAD file, 2026-09-12]
cad/大葱收种一体机/传送带轴固定座2.step
20.0 x 27.0 x 35.0 mm
