Liiiin-hku/smart-scallion-harvester-planter/cad/大葱收种一体机/松土型材支架.step

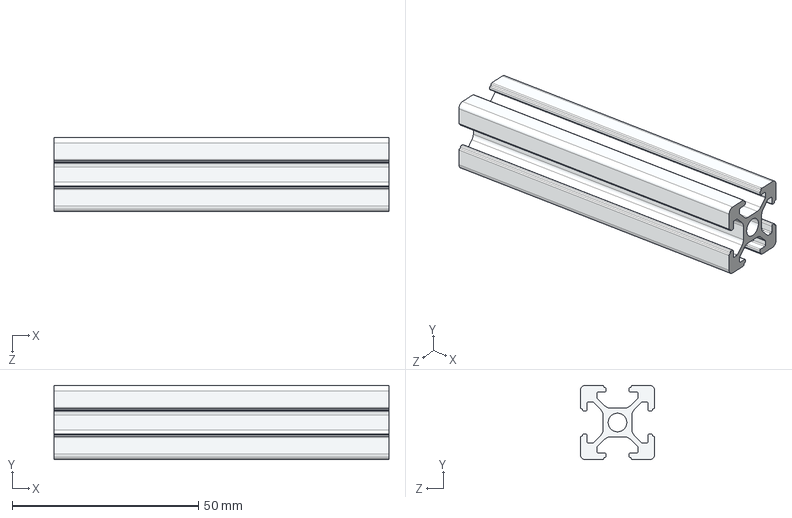
[picture p74: CAD file, 2026-09-12]
cad/大葱收种一体机/松土型材支架.step
90.0 x 20.0 x 20.0 mm
