Liiiin-hku/smart-scallion-harvester-planter/cad/大葱收种一体机/杆端F-M8X125U.step

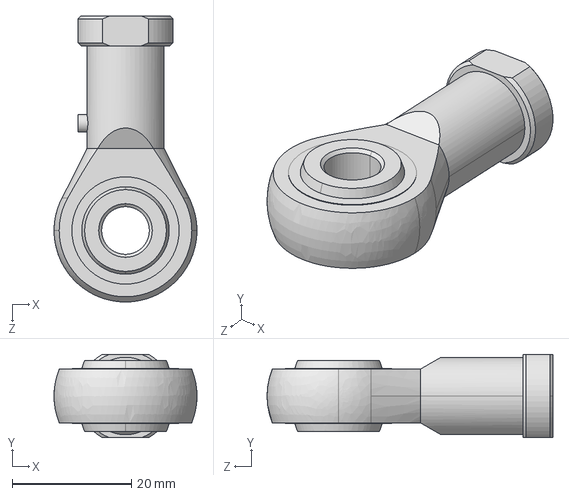
[picture p76: CAD file, 2026-09-12]
cad/大葱收种一体机/杆端F-M8X125U.step
24.0 x 14.0 x 48.0 mm
