Liiiin-hku/smart-scallion-harvester-planter/cad/大葱收种一体机/起垄座.step

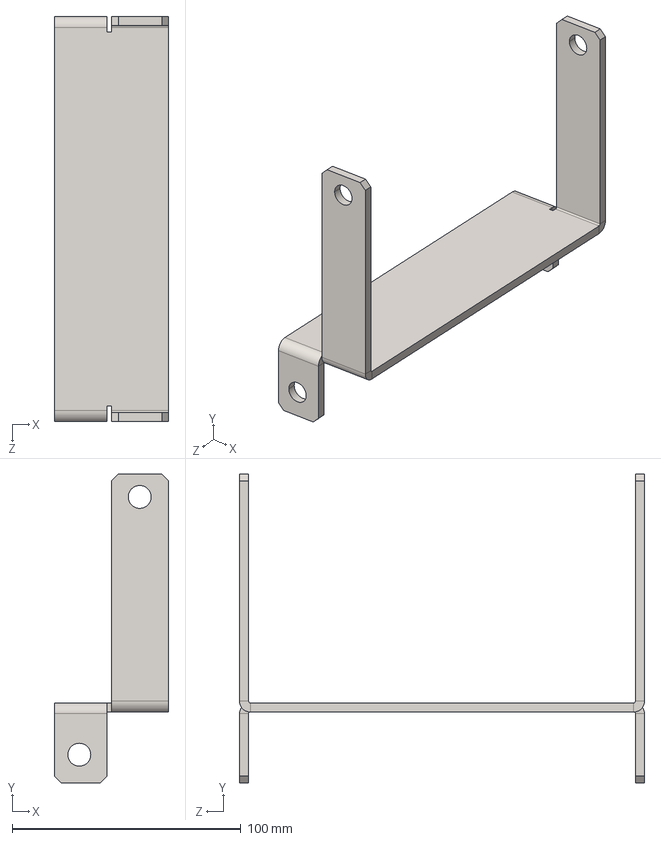
[picture p77: CAD file, 2026-09-12]
cad/大葱收种一体机/起垄座.step
50.0 x 135.0 x 177.0 mm
