Liiiin-hku/smart-scallion-harvester-planter/cad/大葱收种一体机/储存箱子支撑.step

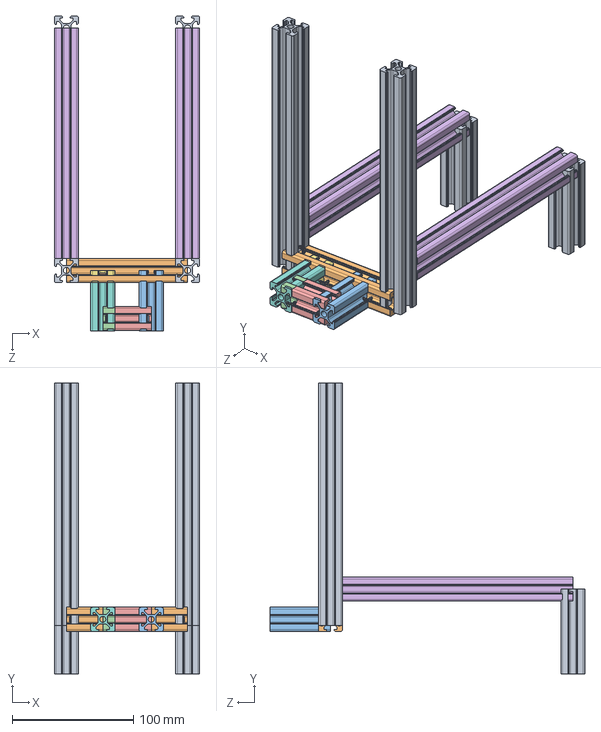
[picture p78: CAD file, 2026-09-12]
cad/大葱收种一体机/储存箱子支撑.step
120.0 x 240.0 x 260.0 mm
