Liiiin-hku/smart-scallion-harvester-planter/cad/大葱收种一体机/固定座.step

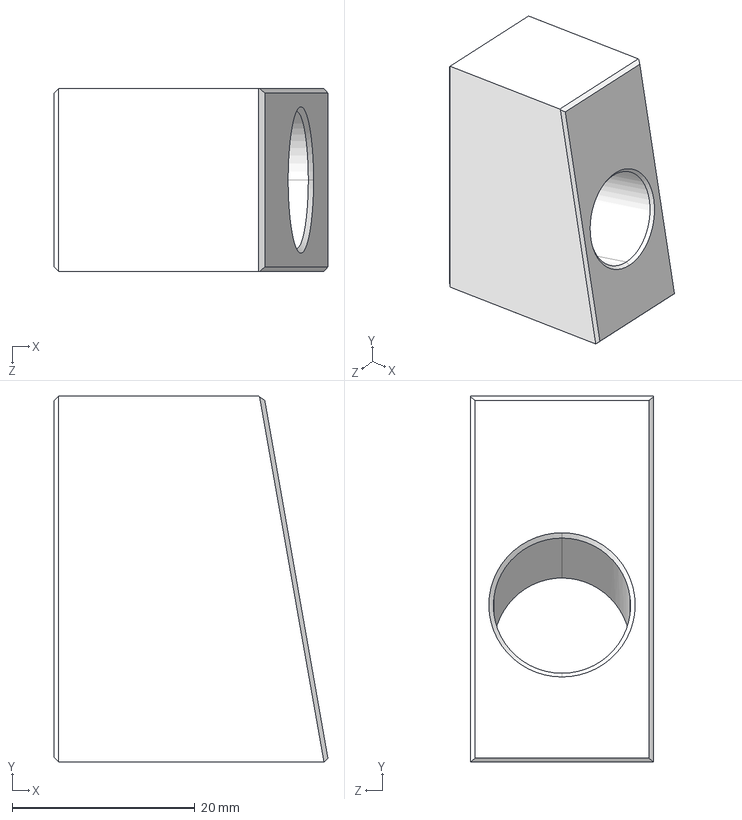
[picture p79: CAD file, 2026-09-12]
cad/大葱收种一体机/固定座.step
29.9 x 40.0 x 20.0 mm
