Liiiin-hku/smart-scallion-harvester-planter/cad/大葱收种一体机/负重轮座.step

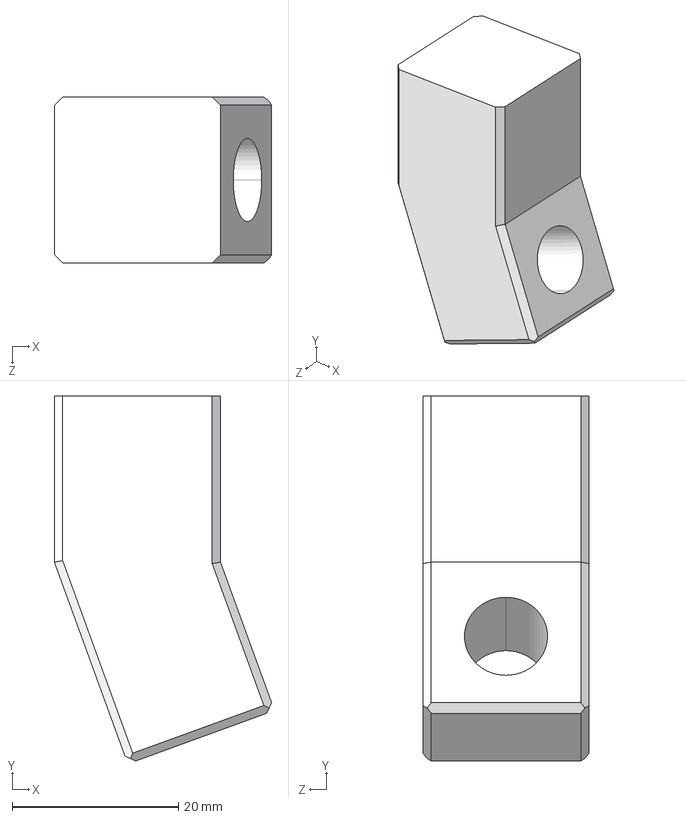
[picture p80: CAD file, 2026-09-12]
cad/大葱收种一体机/负重轮座.step
26.2 x 43.9 x 20.0 mm
