Liiiin-hku/smart-scallion-harvester-planter/cad/大葱收种一体机/清土刷轮.step

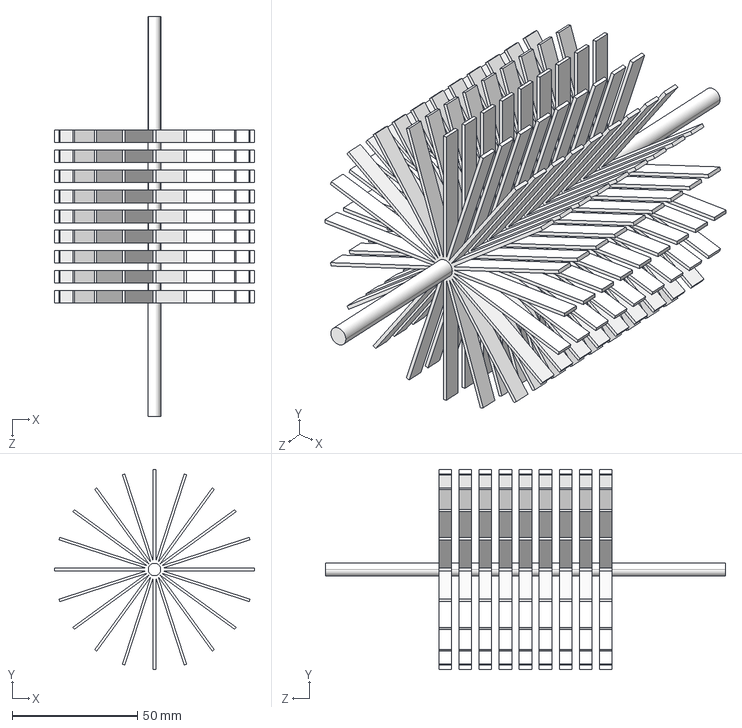
[picture p81: CAD file, 2026-09-12]
cad/大葱收种一体机/清土刷轮.step
80.0 x 80.0 x 160.0 mm
