Liiiin-hku/smart-scallion-harvester-planter/cad/大葱收种一体机/开沟.step

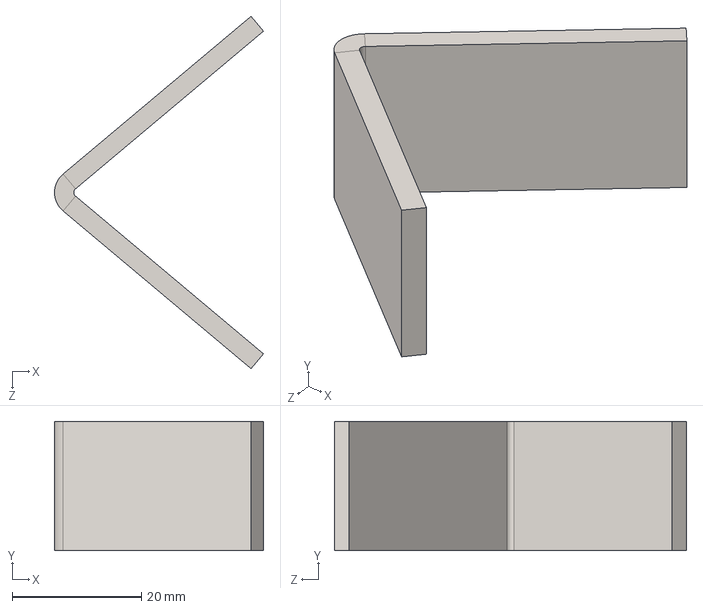
[picture p82: CAD file, 2026-09-12]
cad/大葱收种一体机/开沟.step
32.4 x 20.0 x 54.6 mm
