Liiiin-hku/smart-scallion-harvester-planter/cad/大葱收种一体机/输送带支撑型材.step

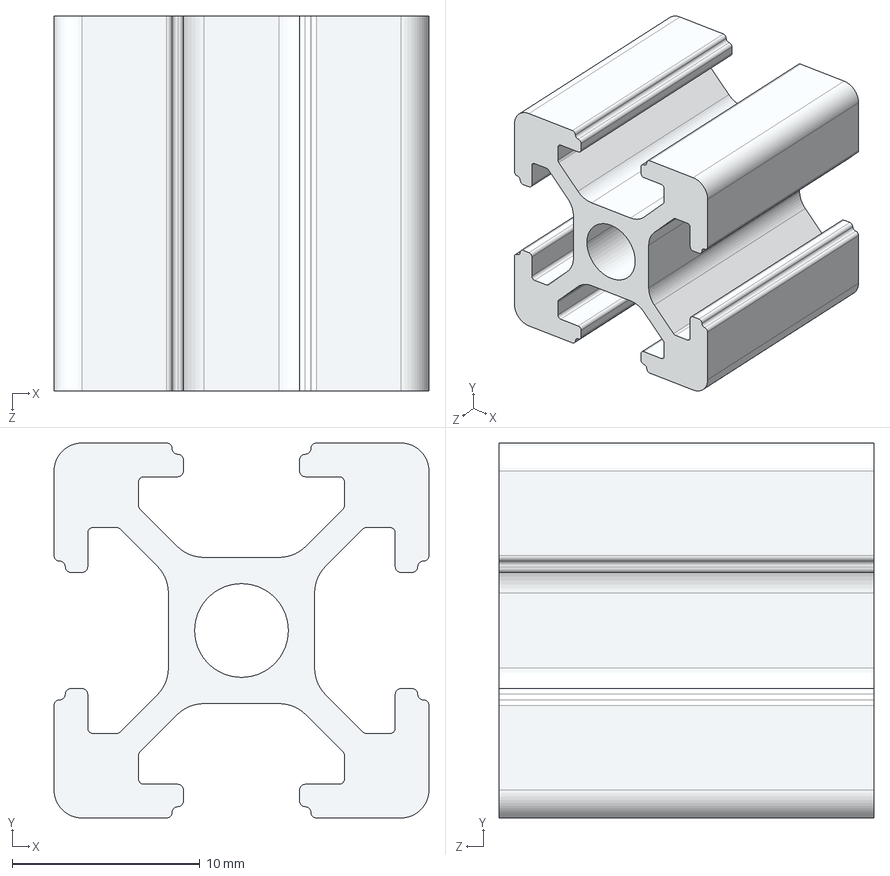
[picture p83: CAD file, 2026-09-12]
cad/大葱收种一体机/输送带支撑型材.step
20.0 x 20.0 x 20.0 mm
