Liiiin-hku/smart-scallion-harvester-planter/cad/大葱收种一体机/轴.step

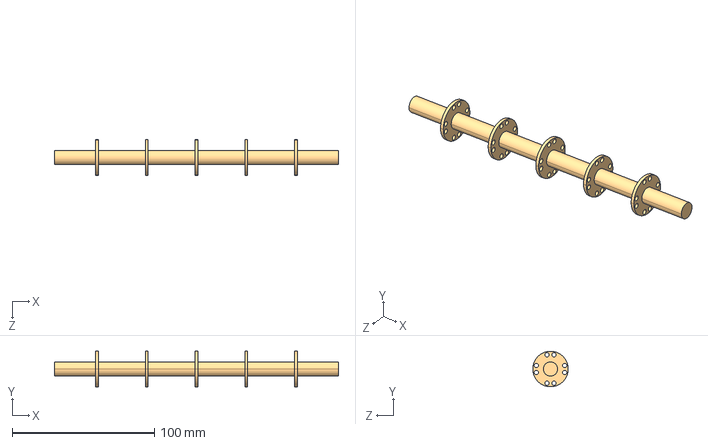
[picture p84: CAD file, 2026-09-12]
cad/大葱收种一体机/轴.step
200.0 x 25.0 x 25.0 mm
