Liiiin-hku/smart-scallion-harvester-planter/cad/大葱收种一体机/清土轮支架支撑型材2.step

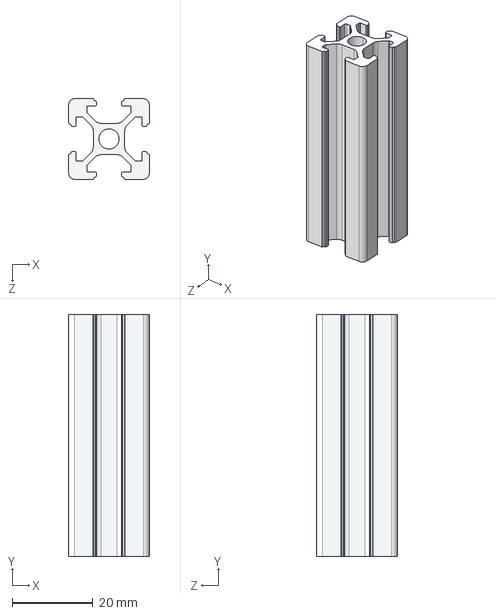
[picture p85: CAD file, 2026-09-12]
cad/大葱收种一体机/清土轮支架支撑型材2.step
20.0 x 60.0 x 20.0 mm
