Liiiin-hku/smart-scallion-harvester-planter/cad/大葱收种一体机/19.AXLE.step

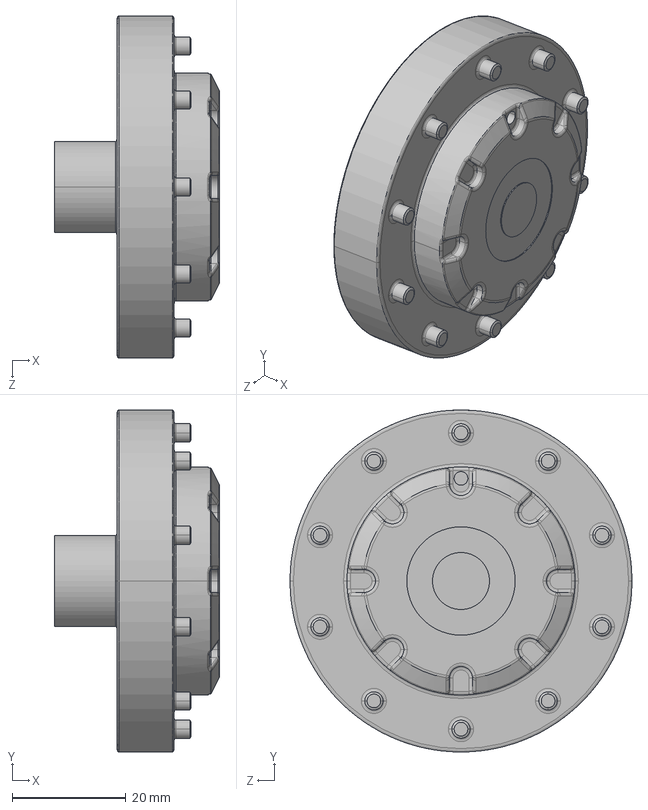
[picture p86: CAD file, 2026-09-12]
cad/大葱收种一体机/19.AXLE.step
29.0 x 60.0 x 60.0 mm
