Liiiin-hku/smart-scallion-harvester-planter/cad/大葱收种一体机/输送带.step

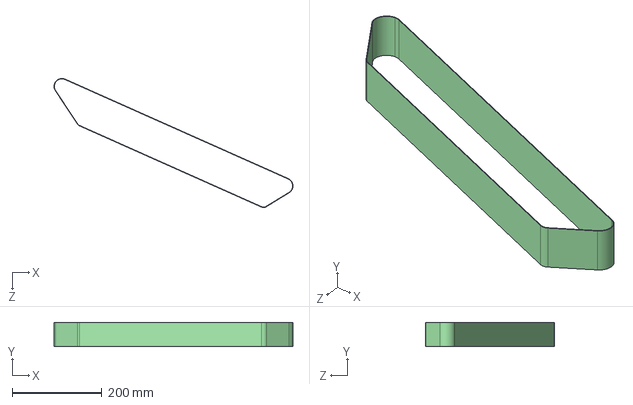
[picture p87: CAD file, 2026-09-12]
cad/大葱收种一体机/输送带.step
532.5 x 54.0 x 287.6 mm
