Liiiin-hku/smart-scallion-harvester-planter/cad/大葱收种一体机/Spike Gribe.step

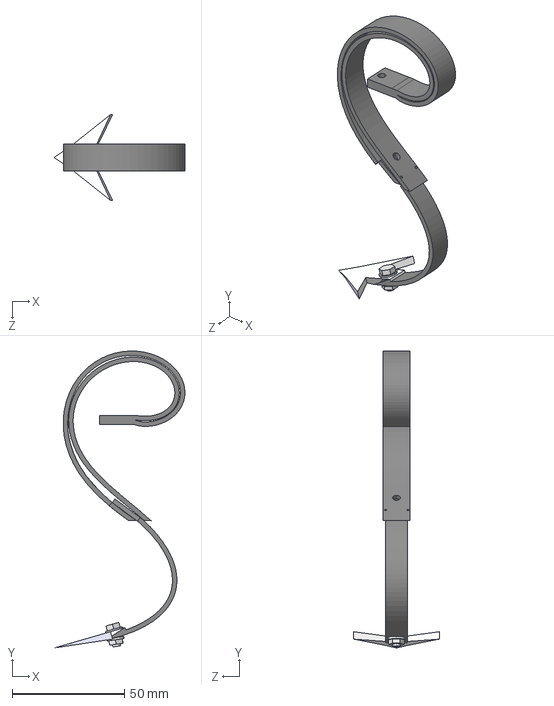
[picture p88: CAD file, 2026-09-12]
cad/大葱收种一体机/Spike Gribe.step
58.4 x 132.5 x 38.3 mm
