Liiiin-hku/smart-scallion-harvester-planter/cad/大葱收种一体机/21. TYRE.step

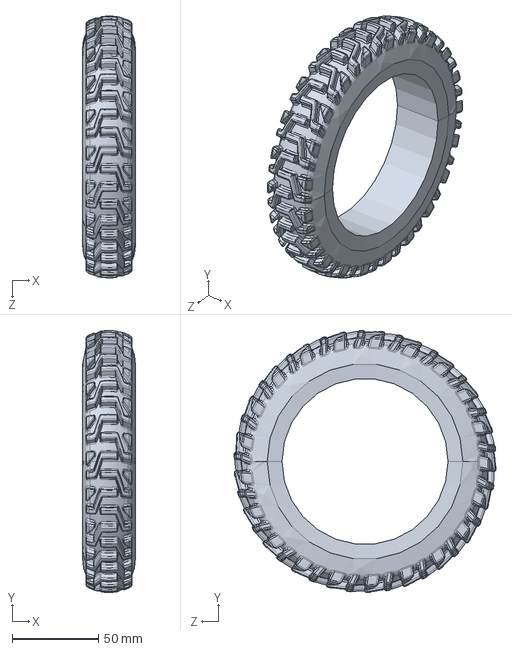
[picture p89: CAD file, 2026-09-12]
cad/大葱收种一体机/21. TYRE.step
30.5 x 151.6 x 151.5 mm
