Liiiin-hku/smart-scallion-harvester-planter/cad/大葱收种一体机/翻土.step

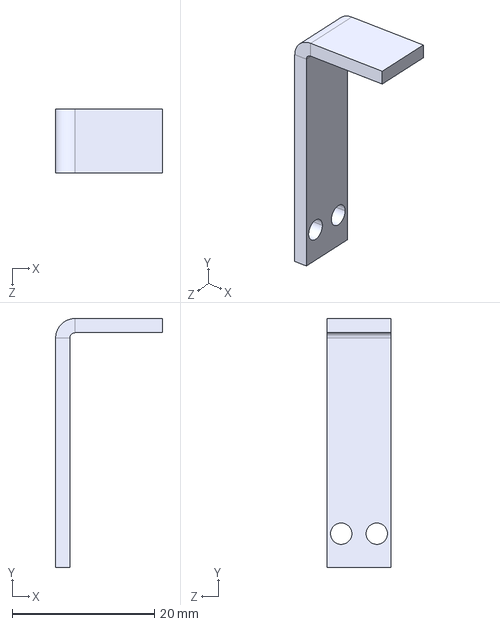
[picture p90: CAD file, 2026-09-12]
cad/大葱收种一体机/翻土.step
15.0 x 35.0 x 9.00 mm
