Liiiin-hku/smart-scallion-harvester-planter/cad/大葱收种一体机/弹簧座.step

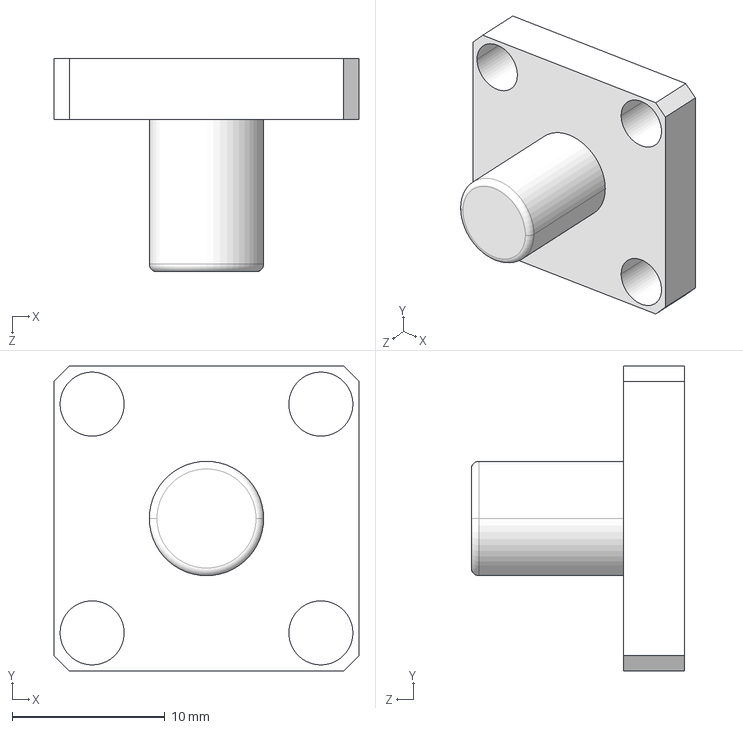
[picture p91: CAD file, 2026-09-12]
cad/大葱收种一体机/弹簧座.step
20.0 x 20.0 x 14.0 mm
