Liiiin-hku/smart-scallion-harvester-planter/cad/大葱收种一体机/20.RIM.step

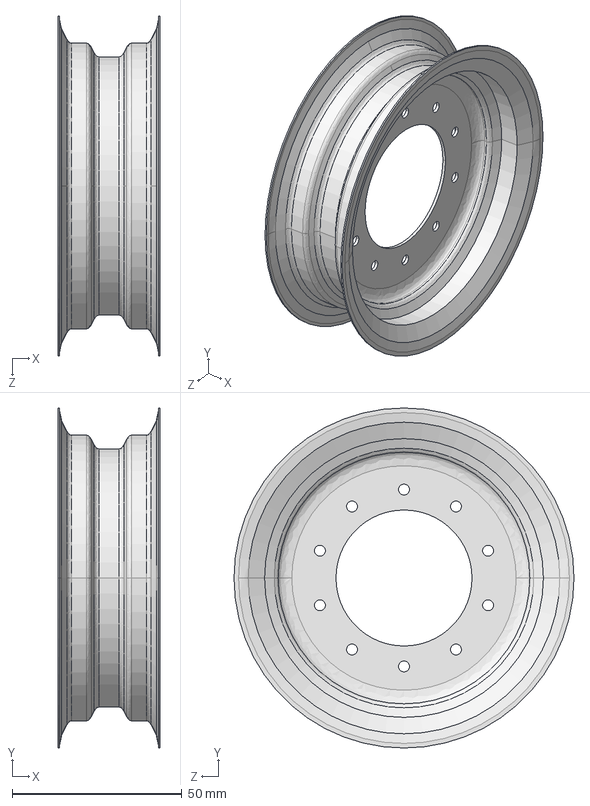
[picture p92: CAD file, 2026-09-12]
cad/大葱收种一体机/20.RIM.step
30.0 x 100.0 x 100.0 mm
