Liiiin-hku/smart-scallion-harvester-planter/cad/大葱收种一体机/收集装置.step

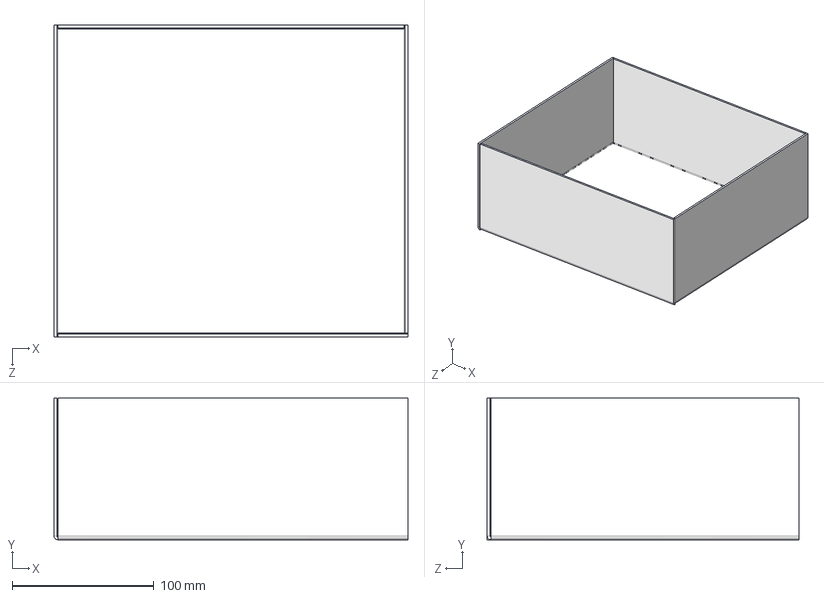
[picture p93: CAD file, 2026-09-12]
cad/大葱收种一体机/收集装置.step
250.0 x 100.0 x 220.0 mm
