Liiiin-hku/smart-scallion-harvester-planter/cad/大葱收种一体机/1X10X50.step

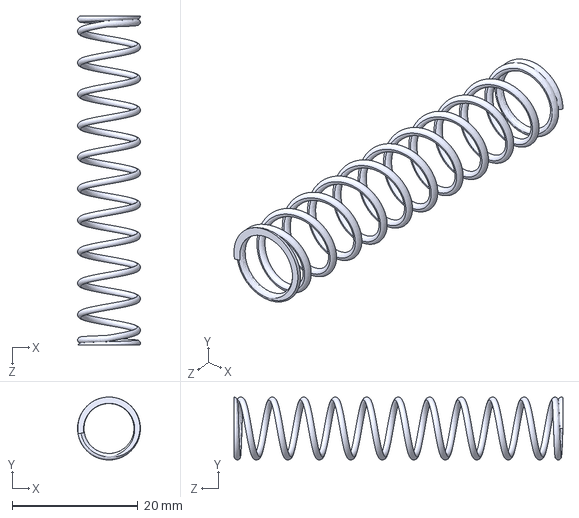
[picture p94: CAD file, 2026-09-12]
cad/大葱收种一体机/1X10X50.step
10.00 x 10.00 x 52.3 mm
