Liiiin-hku/smart-scallion-harvester-planter/cad/大葱收种一体机/松土型材支架2.step

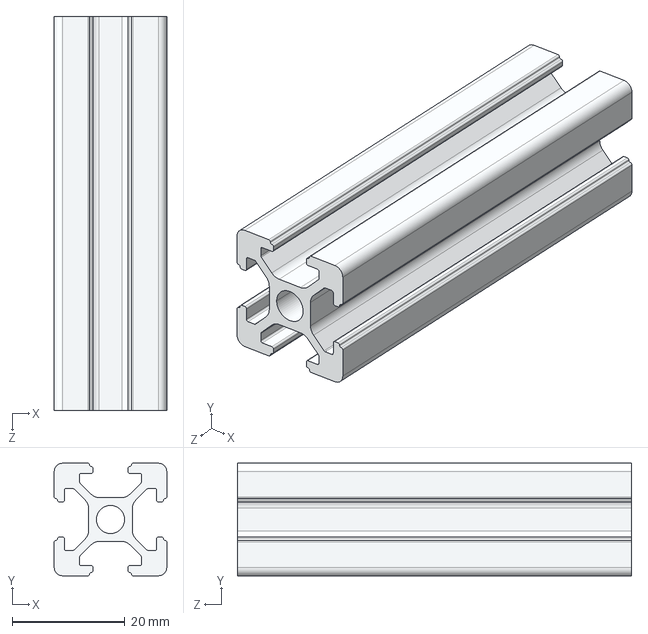
[picture p95: CAD file, 2026-09-12]
cad/大葱收种一体机/松土型材支架2.step
20.0 x 20.0 x 70.0 mm
