Liiiin-hku/smart-scallion-harvester-planter/cad/大葱收种一体机/储存箱子.step

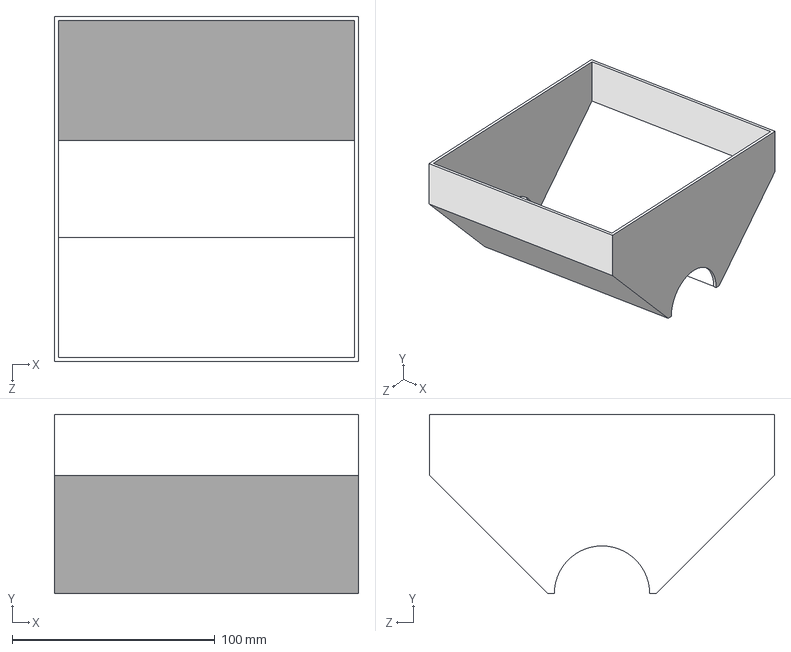
[picture p96: CAD file, 2026-09-12]
cad/大葱收种一体机/储存箱子.step
150.0 x 88.3 x 170.0 mm
